akapustyanik/MZCAT/firmware/Cameras/tamples/right/original quality/h.bmp

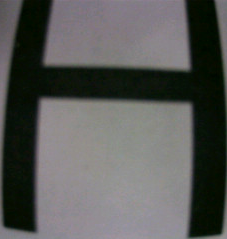
firmware/Cameras/tamples/right/original quality/h.bmp
