akapustyanik/MZCAT/firmware/Cameras/tamples/right/original quality/s.bmp

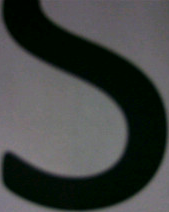
firmware/Cameras/tamples/right/original quality/s.bmp
