akapustyanik/MZCAT/firmware/Cameras/tamples/right/original quality/u.bmp

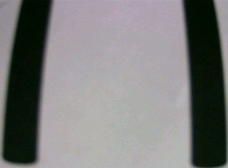
firmware/Cameras/tamples/right/original quality/u.bmp
