akapustyanik/MZCAT/firmware/Cameras/tamples/S_1.bmp

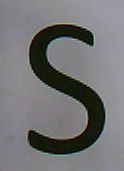
firmware/Cameras/tamples/S_1.bmp
