akapustyanik/MZCAT/photo/robot photo2.jpg

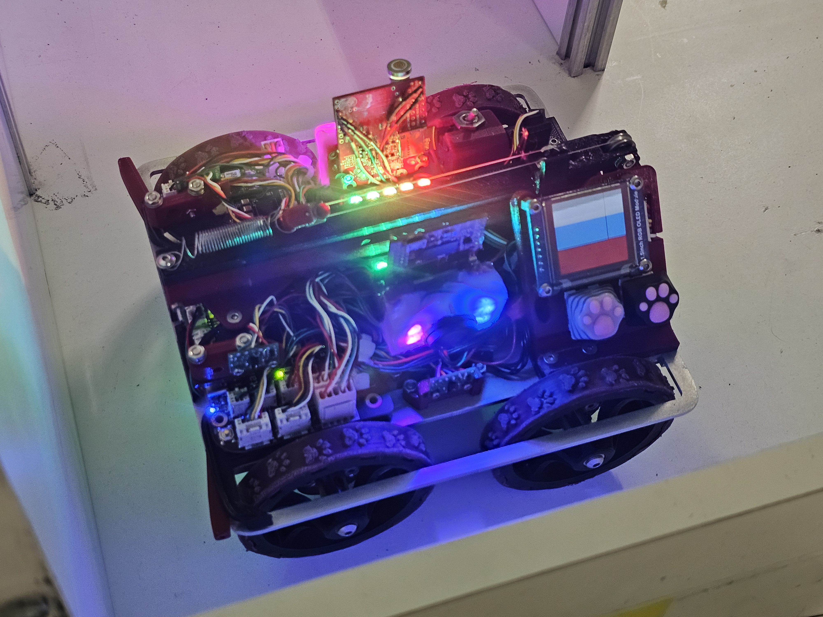
photo/robot photo2.jpg
