akapustyanik/MZCAT/photo/robot photo3.jpg

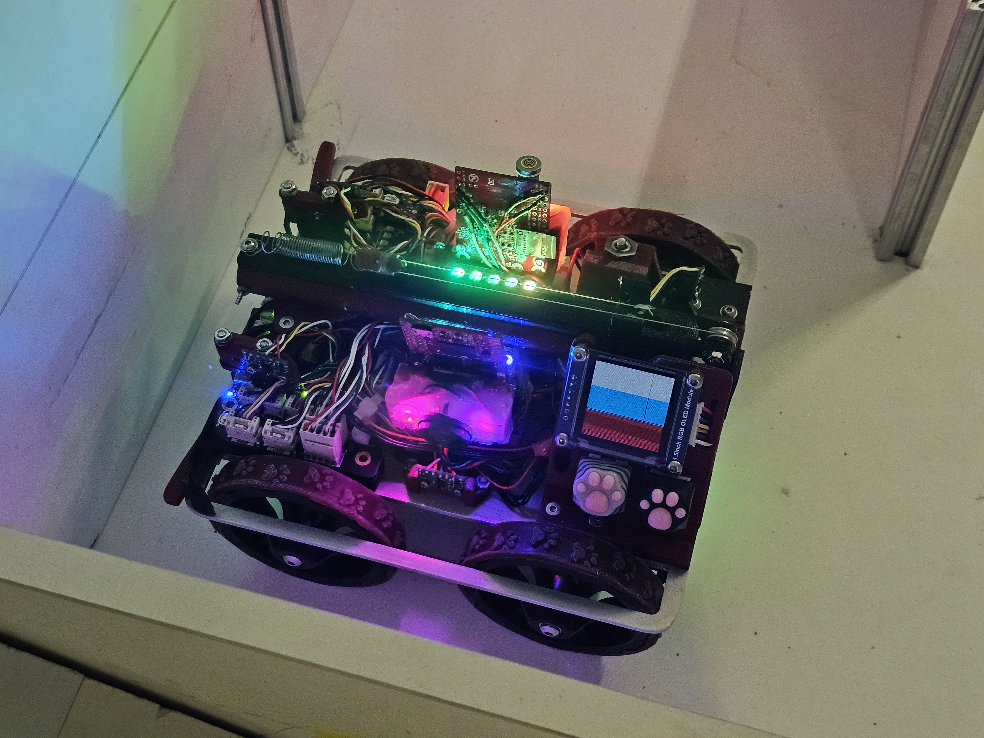
photo/robot photo3.jpg
