akapustyanik/MZCAT/photo/robot photo4.jpg

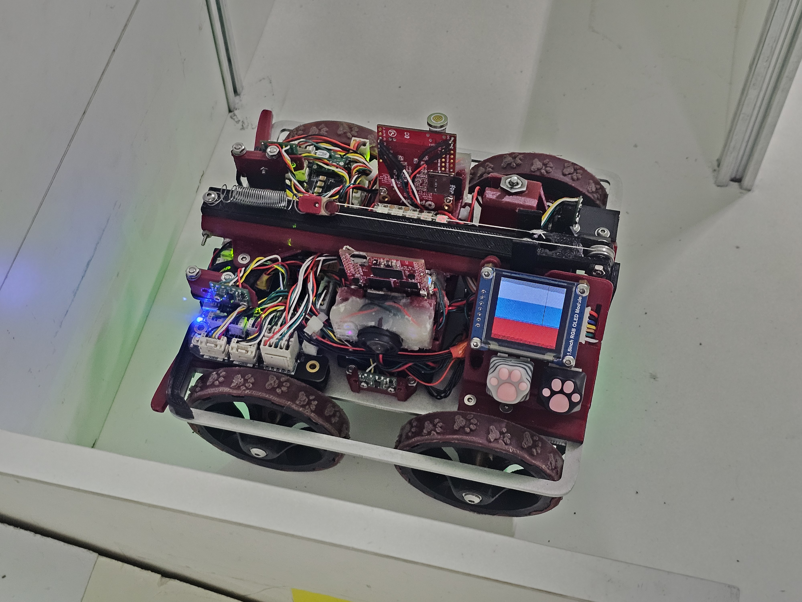
photo/robot photo4.jpg
