akapustyanik/MZCAT/photo/robot photo5.jpg

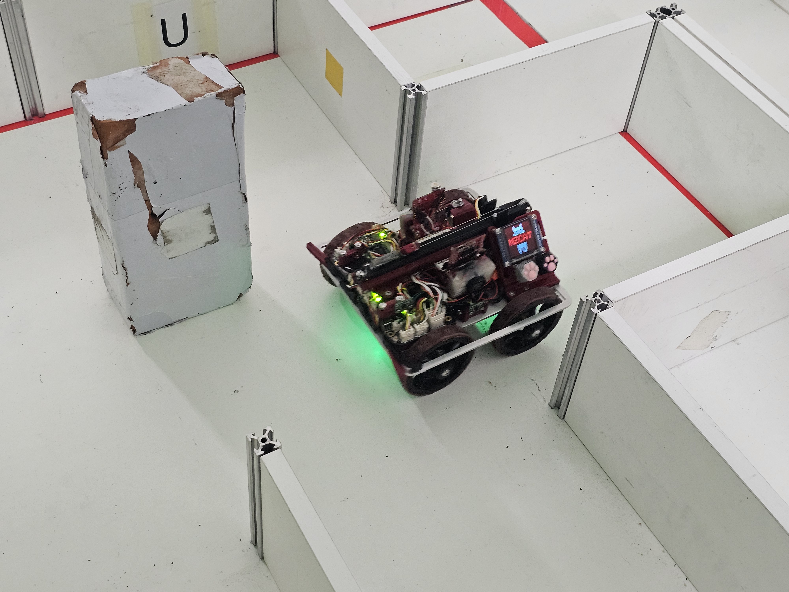
photo/robot photo5.jpg
