akapustyanik/MZCAT/photo/robot photo6.jpg

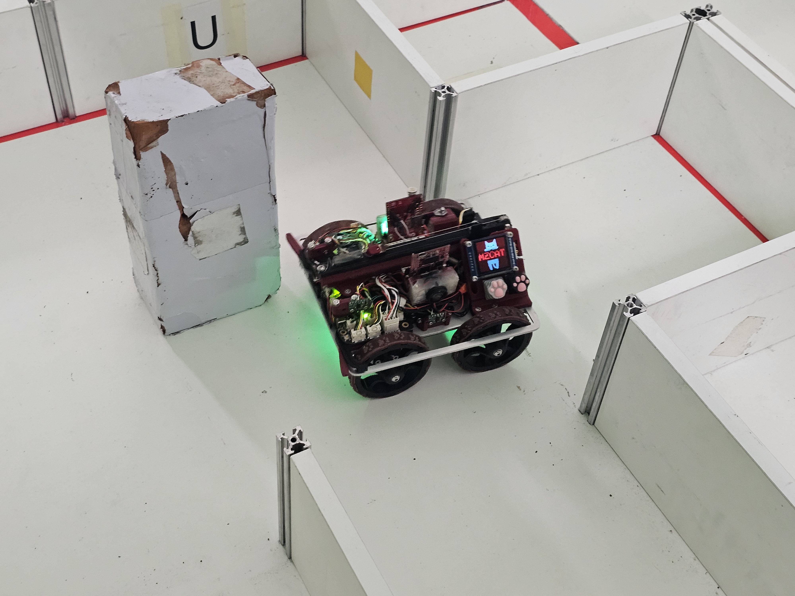
photo/robot photo6.jpg
