akapustyanik/MZCAT/photo/robot photo7.jpg

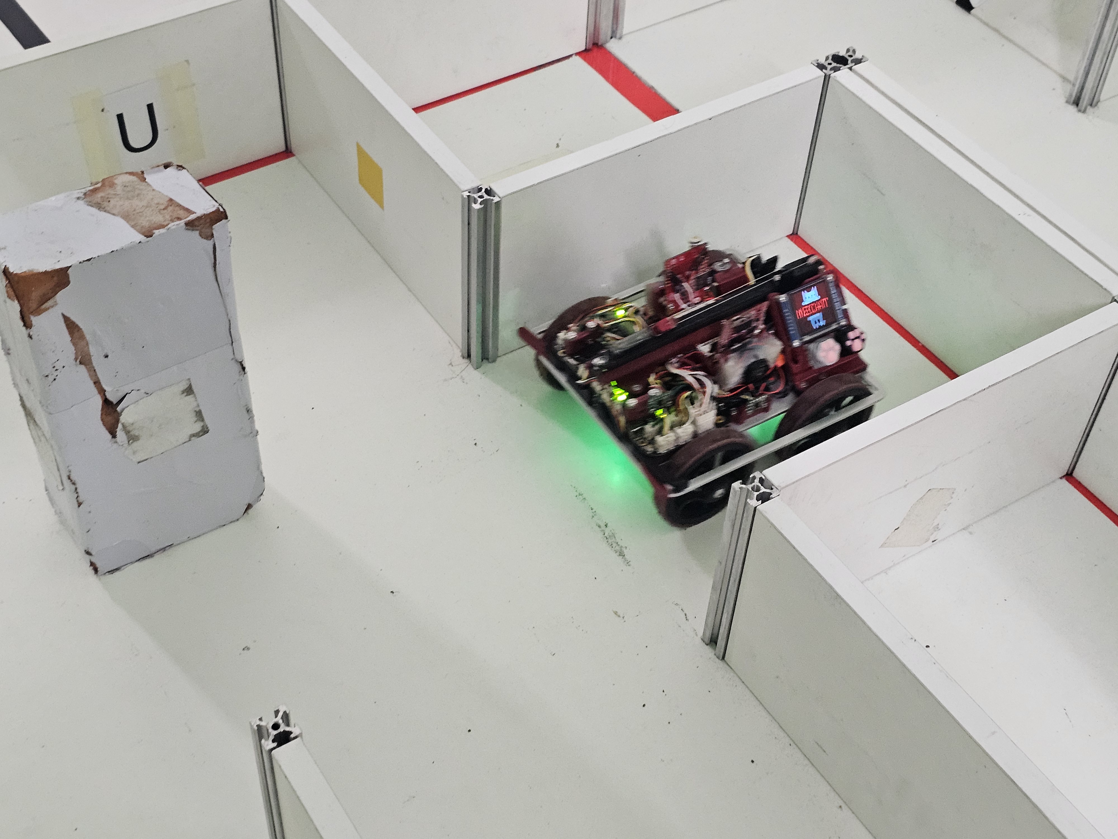
photo/robot photo7.jpg
