akapustyanik/MZCAT/photo/robot photo8.jpg

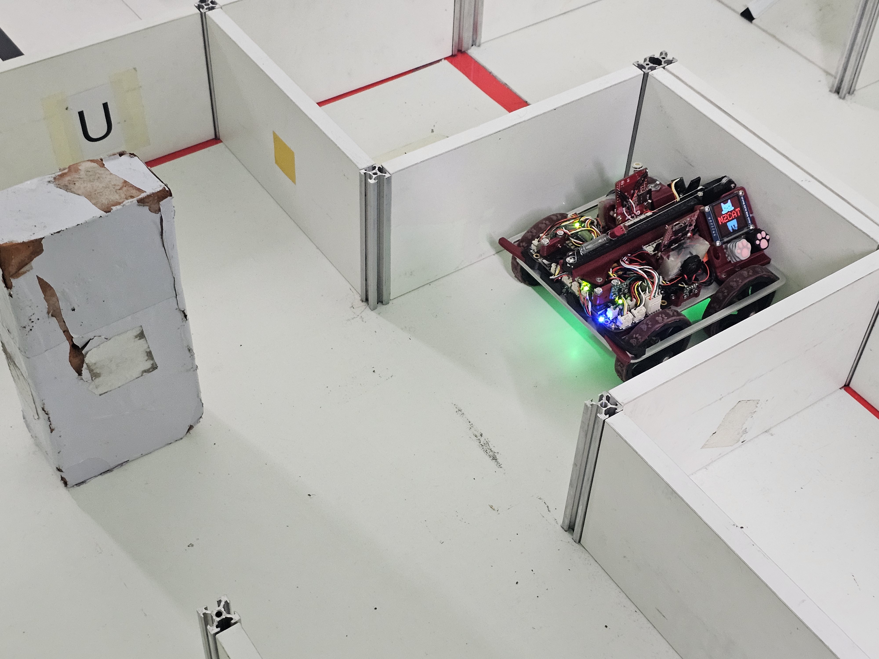
photo/robot photo8.jpg
