akapustyanik/MZCAT/photo/robot photo.jpg

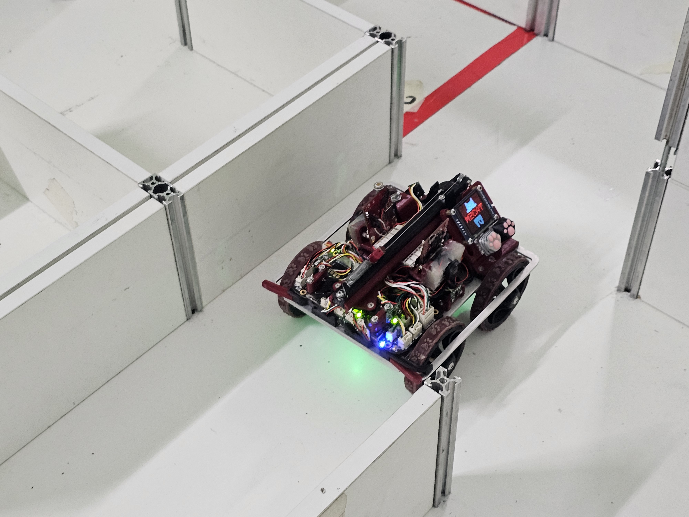
photo/robot photo.jpg
