akapustyanik/MZCAT/Construction/other_models/OpenMV H7/Components/Micro USB socket/UJ2-MIBH2-4-SMT_02.SLDPRT

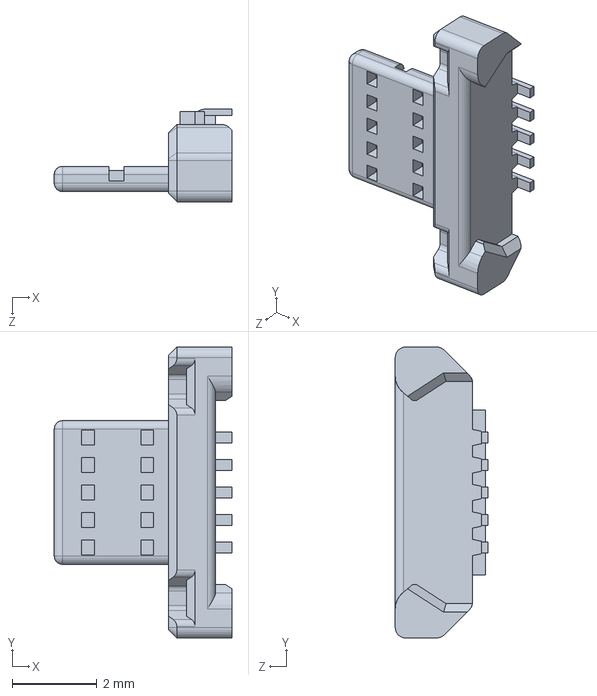
[picture p29: CAD file, 2024-03-27]
Construction/other_models/OpenMV H7/Components/Micro USB socket/UJ2-MIBH2-4-SMT_02.SLDPRT
4.20 x 6.88 x 2.19 mm
