akapustyanik/MZCAT/Construction/other_models/OpenMV H7/Components/standoffs/Standoff metal 5x2.5mm.SLDPRT

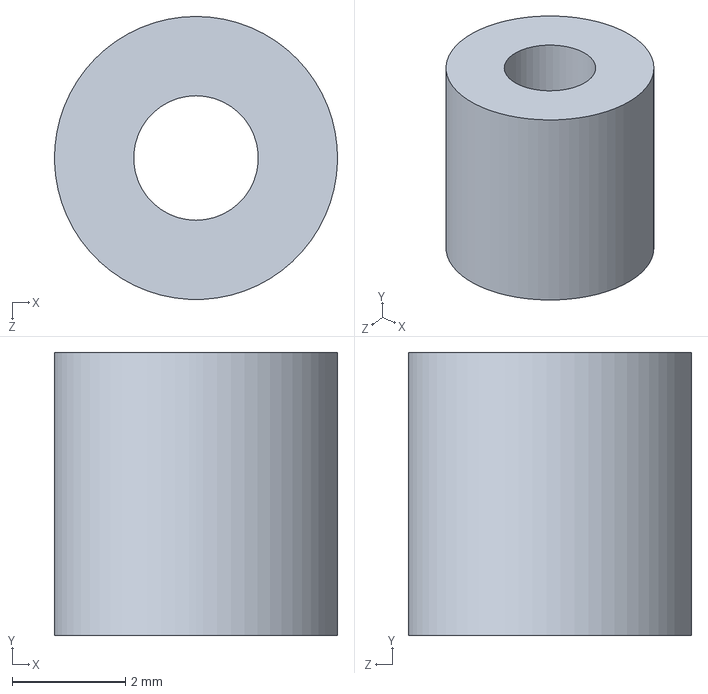
[picture p30: CAD file, 2024-03-27]
Construction/other_models/OpenMV H7/Components/standoffs/Standoff metal 5x2.5mm.SLDPRT
5.00 x 5.00 x 5.00 mm
