akapustyanik/MZCAT/Construction/other_models/OpenMV H7/Components/USB/Micro USB connector.SLDPRT

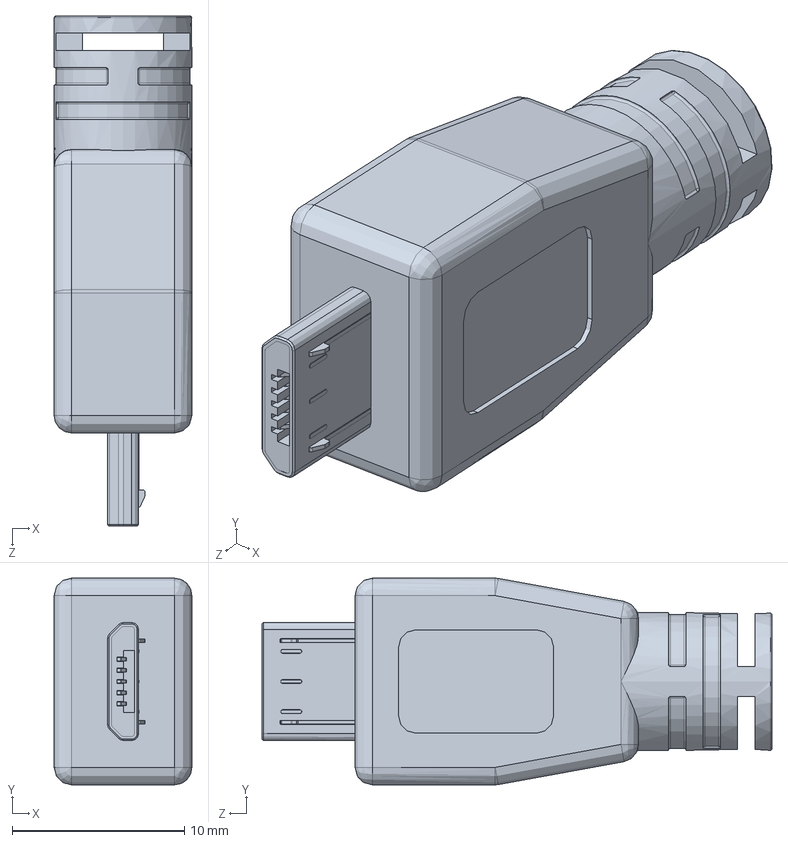
[picture p31: CAD file, 2024-03-27]
Construction/other_models/OpenMV H7/Components/USB/Micro USB connector.SLDPRT
8.00 x 12.0 x 29.6 mm
