akapustyanik/MZCAT/Construction/other_models/vl53l0x/vl53l0x no headers.STEP

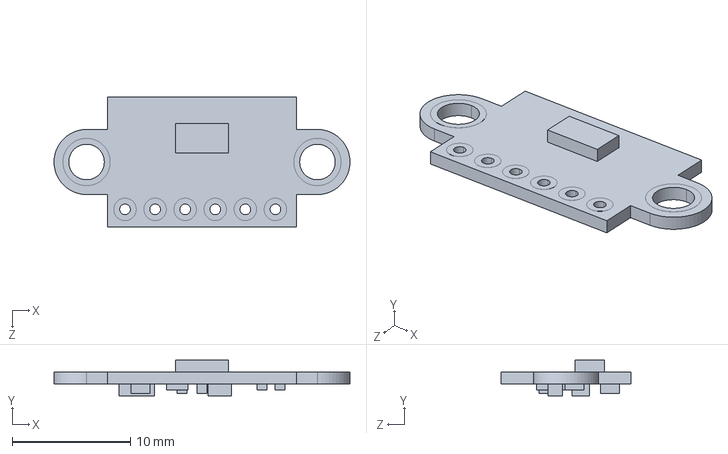
[picture p32: CAD file, 2024-03-27]
Construction/other_models/vl53l0x/vl53l0x no headers.STEP
25.0 x 3.00 x 11.0 mm
