akapustyanik/MZCAT/Construction/step/User Library-xt30-f.step

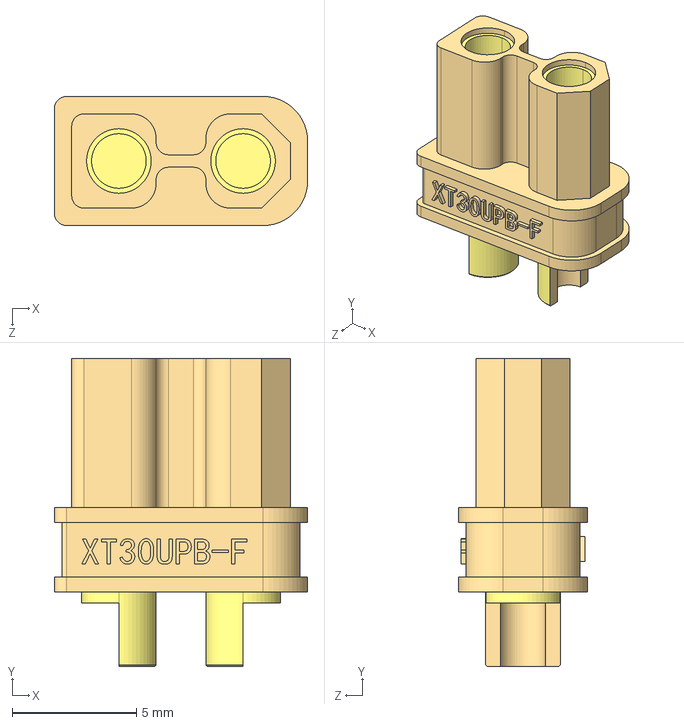
[picture p33: CAD file, 2024-03-27]
Construction/step/User Library-xt30-f.step
10.2 x 12.4 x 5.20 mm
