akapustyanik/MZCAT/Construction/stl/karetka.stl

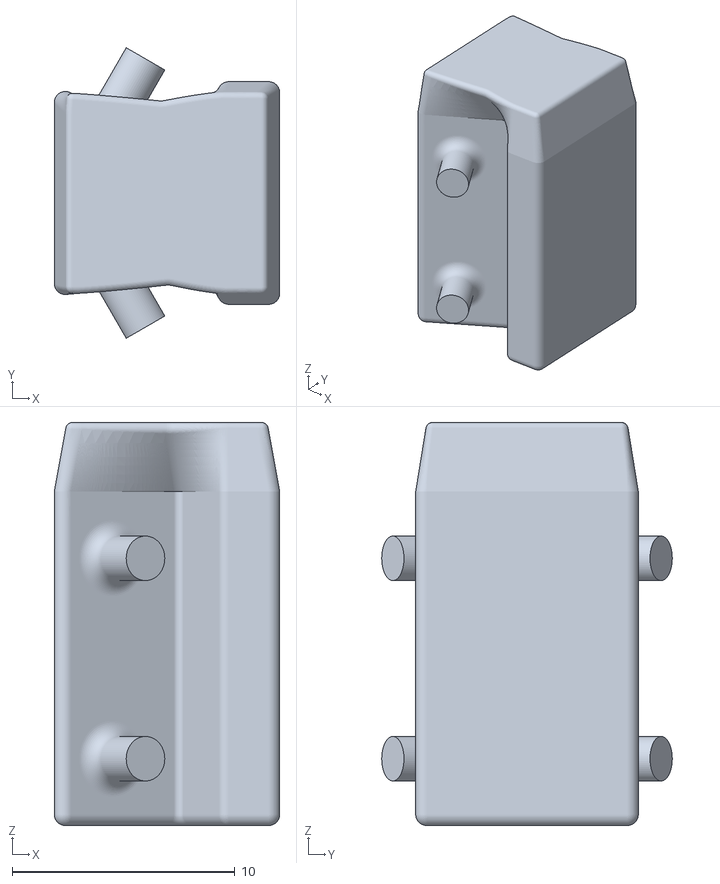
[picture p34: CAD file, 2024-03-27]
Construction/stl/karetka.stl
10.1 x 13.0 x 18.1
