akapustyanik/MZCAT/Construction/dxf/maze_4.dxf

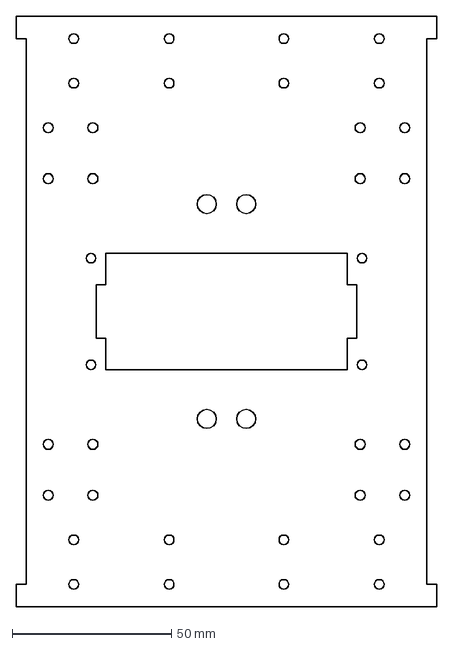
[picture p35: CAD file, 2024-03-27]
Construction/dxf/maze_4.dxf
132.0 x 185.5 mm
