akapustyanik/MZCAT/Construction/other_models/OpenMV H7/Boards/ov7725.sldprt

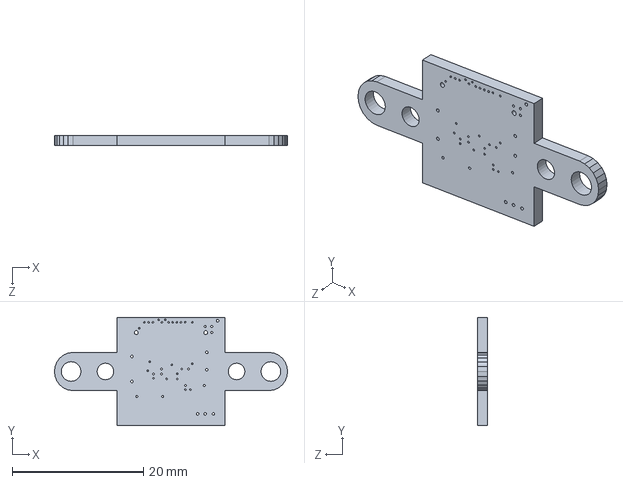
[picture p36: CAD file, 2024-03-27]
Construction/other_models/OpenMV H7/Boards/ov7725.sldprt
35.6 x 16.5 x 1.60 mm
