akapustyanik/MZCAT/Construction/other_models/OpenMV H7/Components/Camera_20mm/mount_lens.SLDPRT

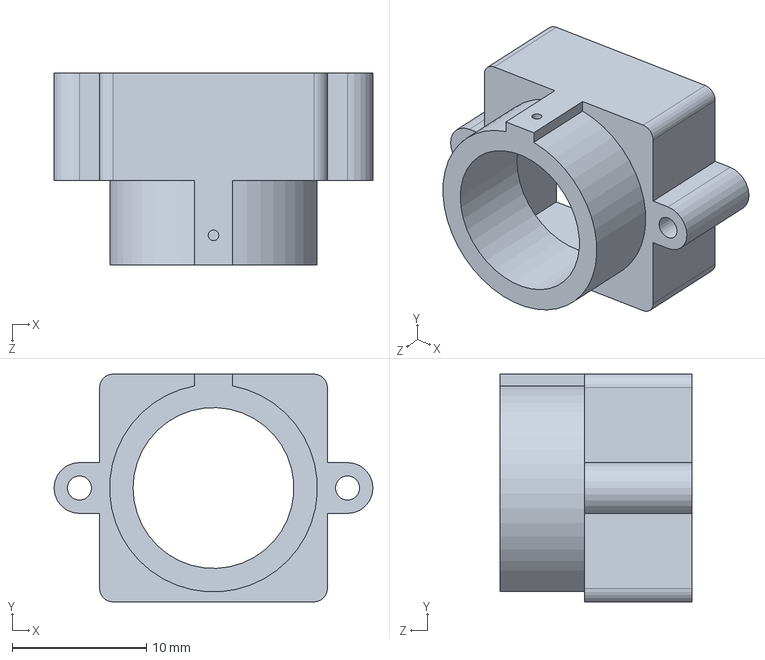
[picture p37: CAD file, 2024-03-27]
Construction/other_models/OpenMV H7/Components/Camera_20mm/mount_lens.SLDPRT
23.8 x 17.0 x 14.3 mm
