akapustyanik/MZCAT/Construction/other_models/OpenMV H7/Components/Micro USB socket/UJ2-MIBH2-4-SMT_01.SLDPRT

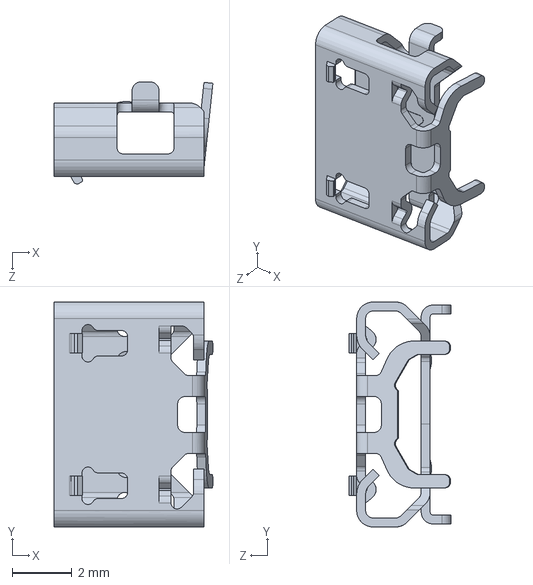
[picture p38: CAD file, 2024-03-27]
Construction/other_models/OpenMV H7/Components/Micro USB socket/UJ2-MIBH2-4-SMT_01.SLDPRT
5.29 x 7.50 x 3.41 mm
