akapustyanik/MZCAT/Construction/other_models/OpenMV H7/Components/Resistor 0603.SLDPRT

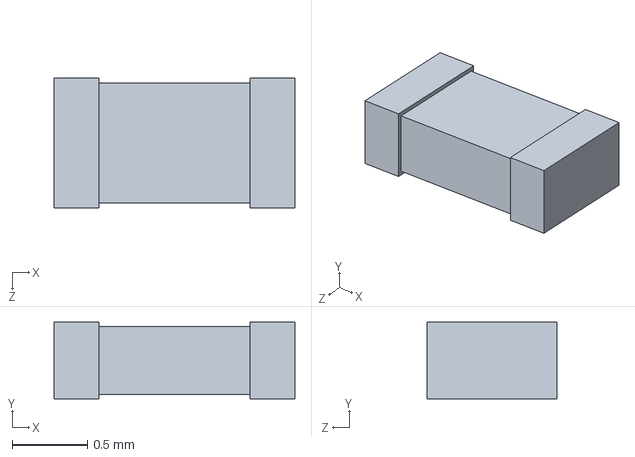
[picture p39: CAD file, 2024-03-27]
Construction/other_models/OpenMV H7/Components/Resistor 0603.SLDPRT
1.60 x 0.51 x 0.86 mm
