akapustyanik/MZCAT/Construction/other_models/OpenMV H7/Components/USB/Micro USB connector angle.SLDPRT

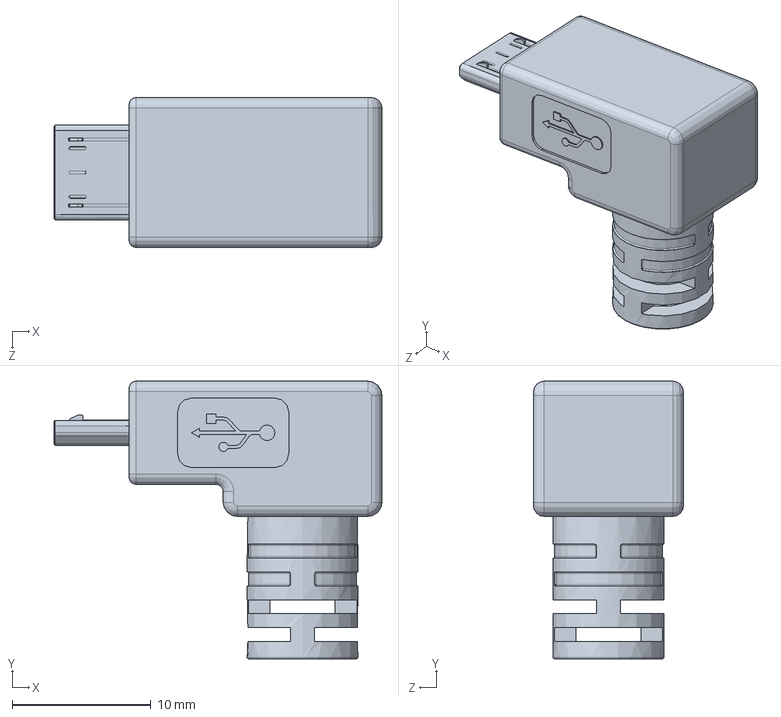
[picture p40: CAD file, 2024-03-27]
Construction/other_models/OpenMV H7/Components/USB/Micro USB connector angle.SLDPRT
23.6 x 20.0 x 10.8 mm
