akapustyanik/MZCAT/Construction/other_models/vl53l0x/pin_header.SLDPRT

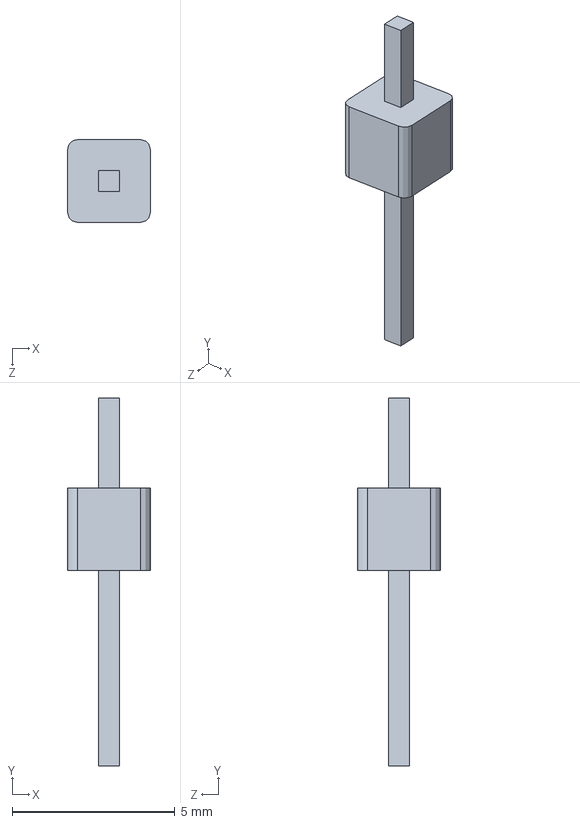
[picture p41: CAD file, 2024-03-27]
Construction/other_models/vl53l0x/pin_header.SLDPRT
2.54 x 11.3 x 2.54 mm
