akapustyanik/MZCAT/Construction/step/kicad_module_3D_MINI560.step

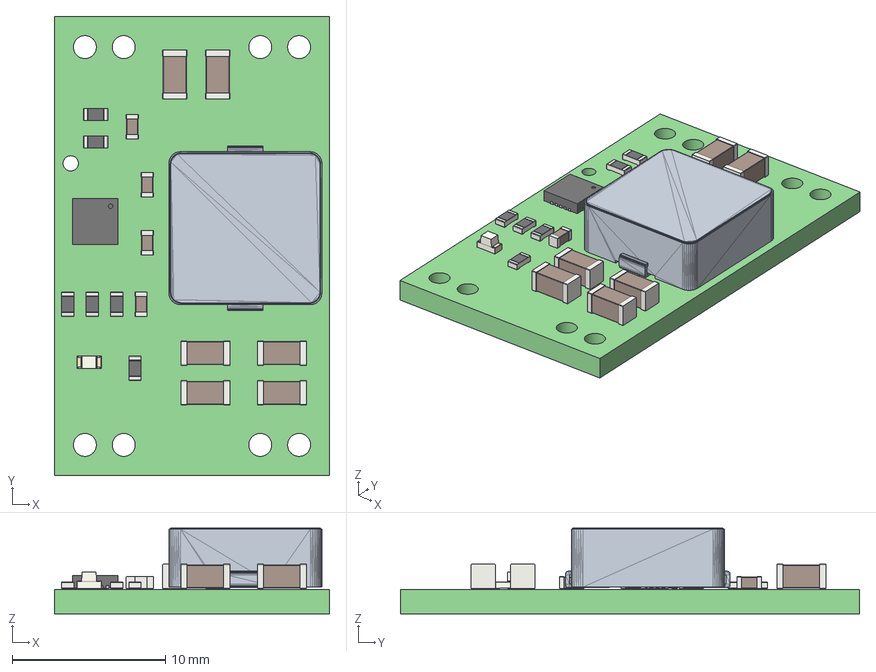
[picture p42: CAD file, 2024-03-27]
Construction/step/kicad_module_3D_MINI560.step
18.0 x 30.0 x 5.62 mm
kicad_module_3D_MINI560 PCB
