akapustyanik/MZCAT/Construction/stl/разделитель.stl

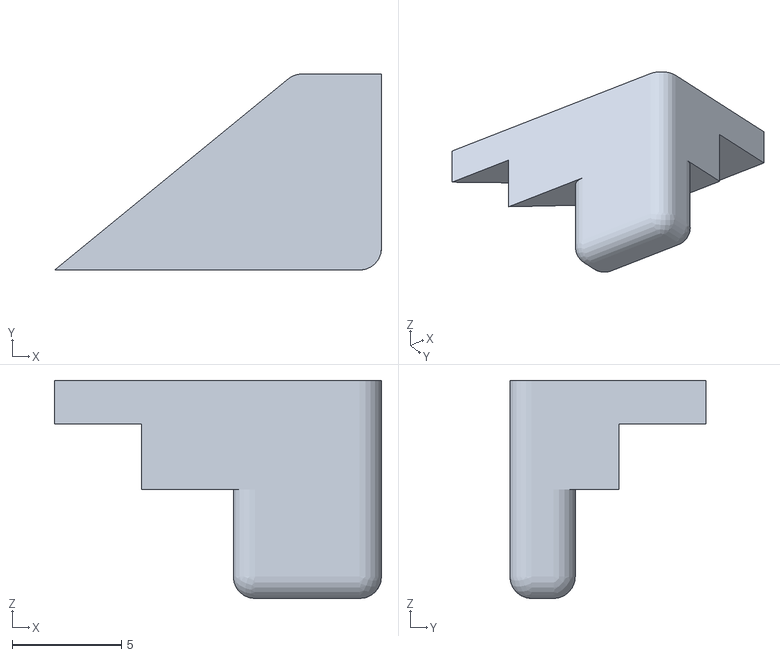
[picture p43: CAD file, 2024-03-27]
Construction/stl/разделитель.stl
15.0 x 9.00 x 10.0
