akapustyanik/MZCAT/Construction/dxf/holder.dxf

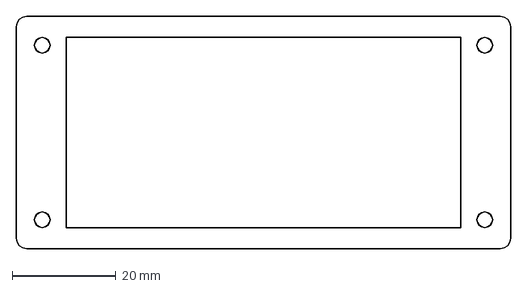
[picture p44: CAD file, 2024-03-27]
Construction/dxf/holder.dxf
95.2 x 44.7 mm
