akapustyanik/MZCAT/Construction/other_models/OpenMV H7/Components/Camera_20mm/LENS_Standard.SLDPRT

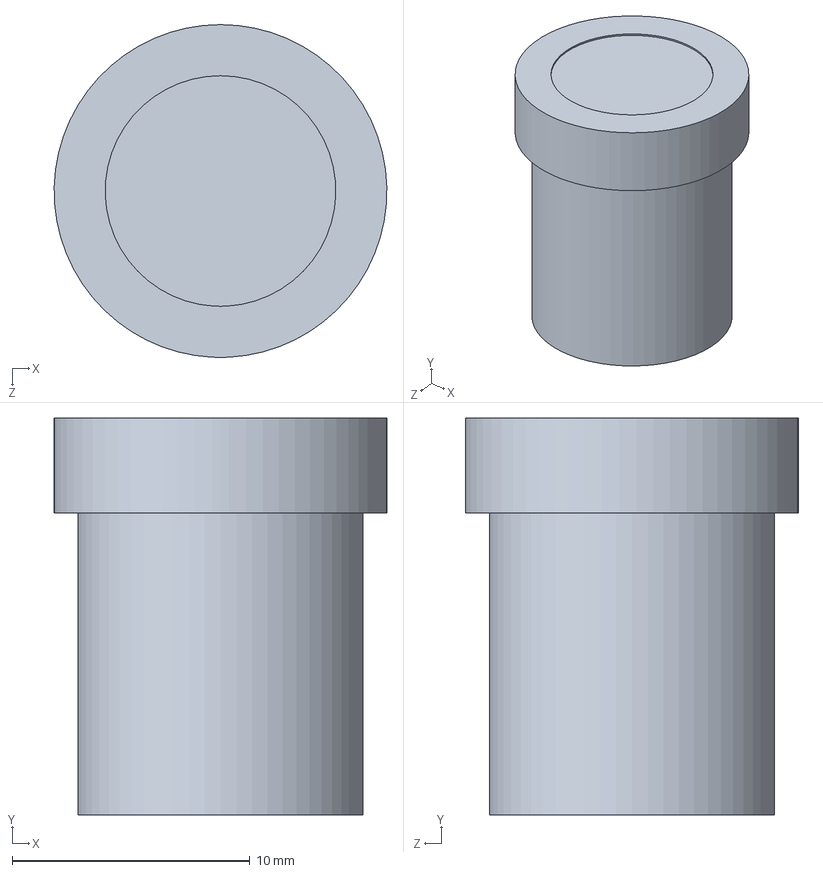
[picture p45: CAD file, 2024-03-27]
Construction/other_models/OpenMV H7/Components/Camera_20mm/LENS_Standard.SLDPRT
14.0 x 16.7 x 14.0 mm
