akapustyanik/MZCAT/Construction/other_models/OpenMV H7/Components/LED 1206 IR.SLDPRT

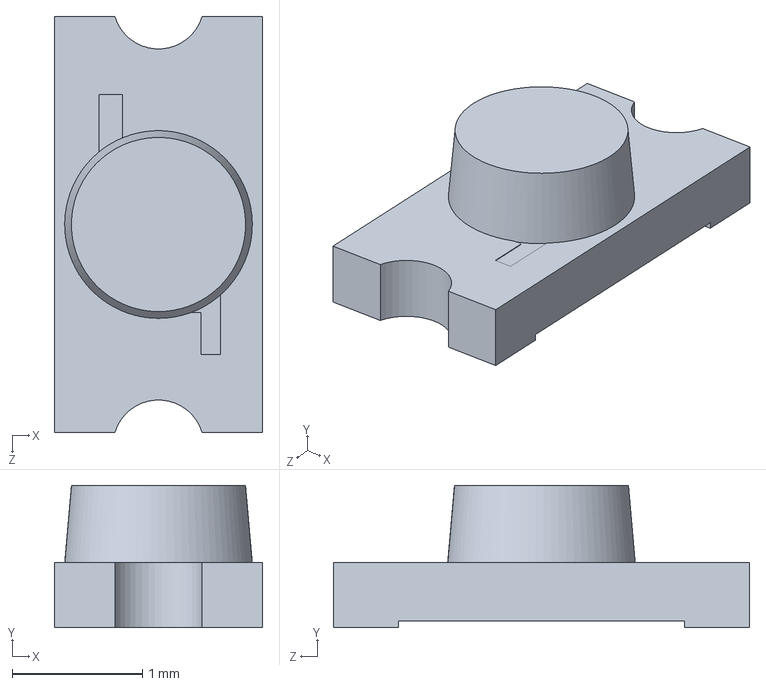
[picture p46: CAD file, 2024-03-27]
Construction/other_models/OpenMV H7/Components/LED 1206 IR.SLDPRT
1.60 x 1.09 x 3.20 mm
