akapustyanik/MZCAT/Construction/other_models/vl53l0x/vl53l0x.STEP

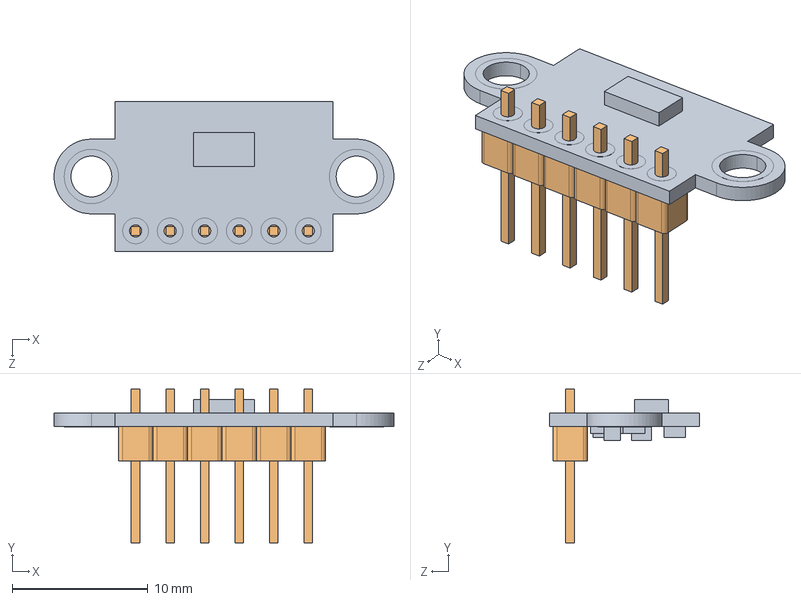
[picture p47: CAD file, 2024-03-27]
Construction/other_models/vl53l0x/vl53l0x.STEP
25.0 x 11.3 x 11.0 mm
vl53l0x_PCB
pin_header x 6
