akapustyanik/MZCAT/Construction/step/clik mate 3.stp

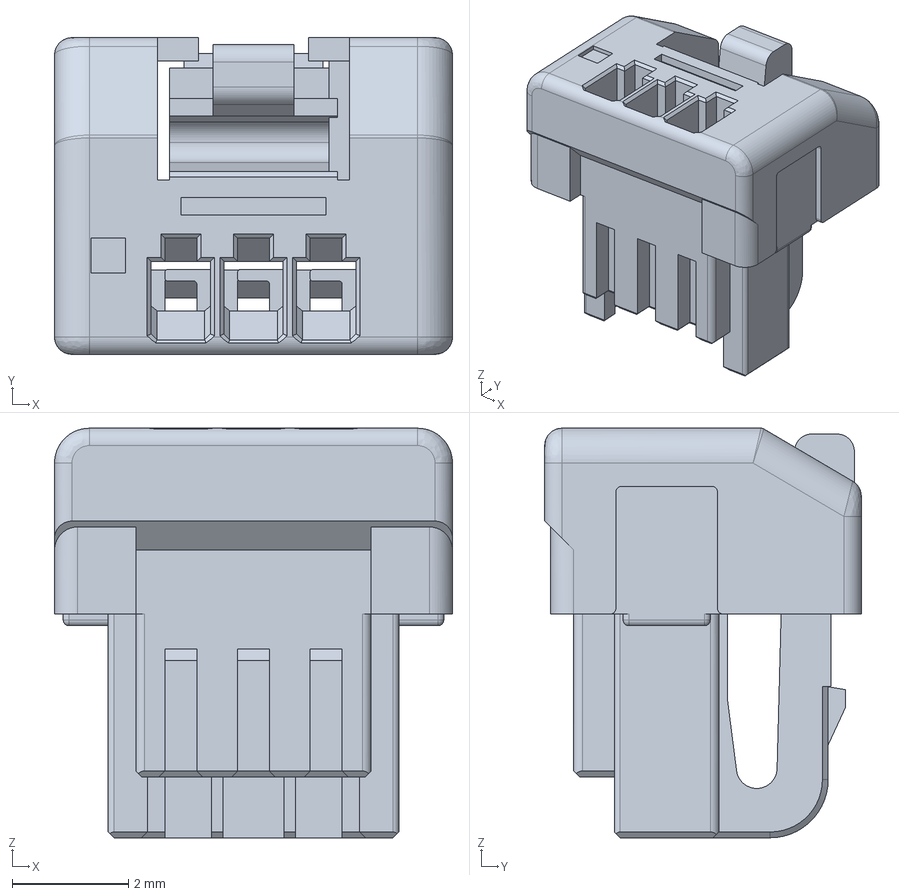
[picture p48: CAD file, 2024-03-27]
Construction/step/clik mate 3.stp
6.85 x 5.45 x 7.05 mm
