akapustyanik/MZCAT/Construction/stl/laser_krepl_2.stl

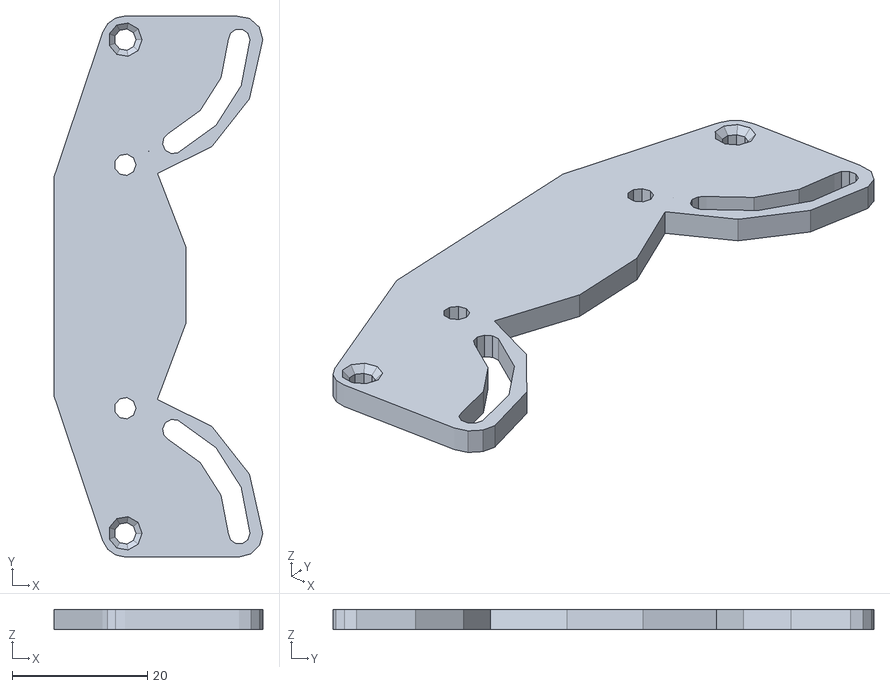
[picture p49: CAD file, 2024-03-27]
Construction/stl/laser_krepl_2.stl
30.9 x 80.0 x 3.00
