akapustyanik/MZCAT/Construction/dxf/protection_frame2.dxf

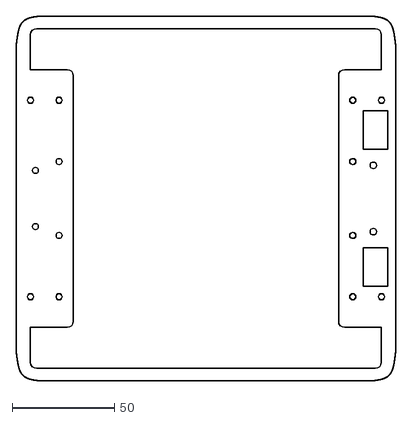
[picture p50: CAD file, 2024-03-27]
Construction/dxf/protection_frame2.dxf
185.5 x 178.0
