akapustyanik/MZCAT/Construction/step/light_sensor.step

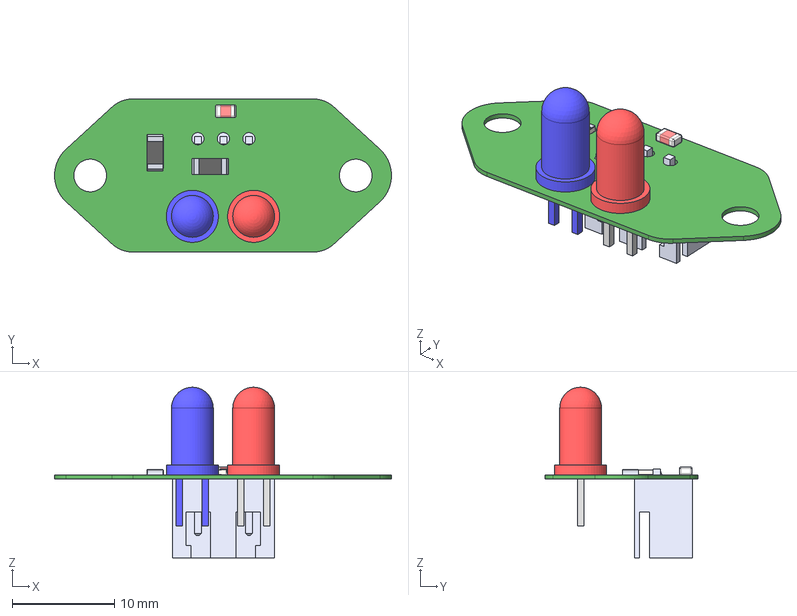
[picture p51: CAD file, 2024-03-27]
Construction/step/light_sensor.step
33.0 x 15.0 x 16.7 mm
SW3DPS-5MM_LED_RED-DEFAULT
CAP0805
SW3DPS-5MM_LED_RED-DEFAULT_RGB16711680
R1206 x 2
CWF_3_V
