akapustyanik/MZCAT/Construction/stl/end cap left.stl

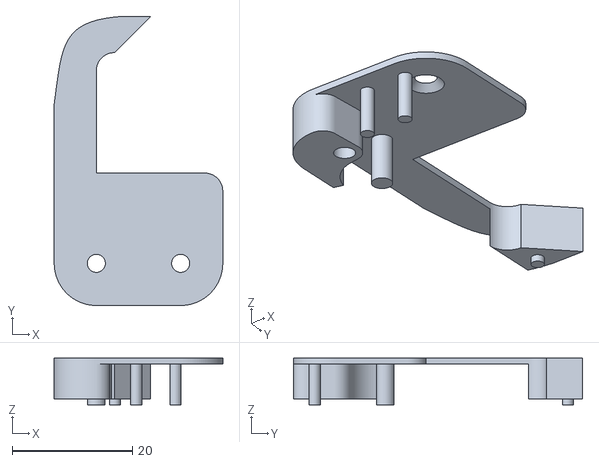
[picture p52: CAD file, 2024-03-27]
Construction/stl/end cap left.stl
28.0 x 48.0 x 7.80
