akapustyanik/MZCAT/Construction/dxf/osvesh2.dxf

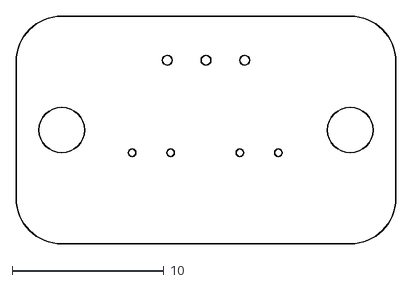
[picture p53: CAD file, 2024-03-27]
Construction/dxf/osvesh2.dxf
25.0 x 15.0
