akapustyanik/MZCAT/Construction/other_models/OpenMV H7/Components/S2B-PH-K-S(LF)(SN).SLDPRT

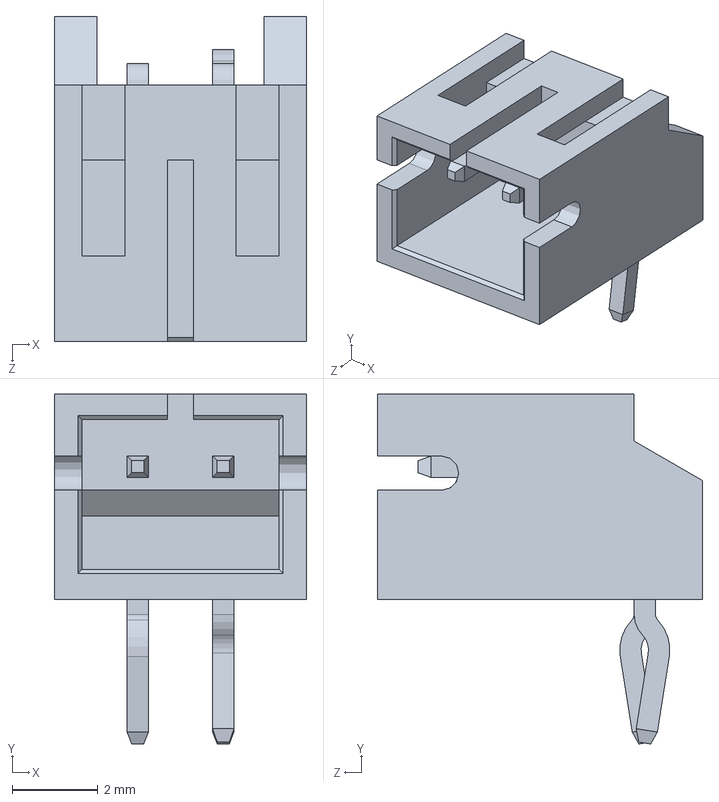
[picture p54: CAD file, 2024-03-27]
Construction/other_models/OpenMV H7/Components/S2B-PH-K-S(LF)(SN).SLDPRT
5.90 x 8.18 x 7.60 mm
