akapustyanik/MZCAT/Construction/stl/pizza_2.stl

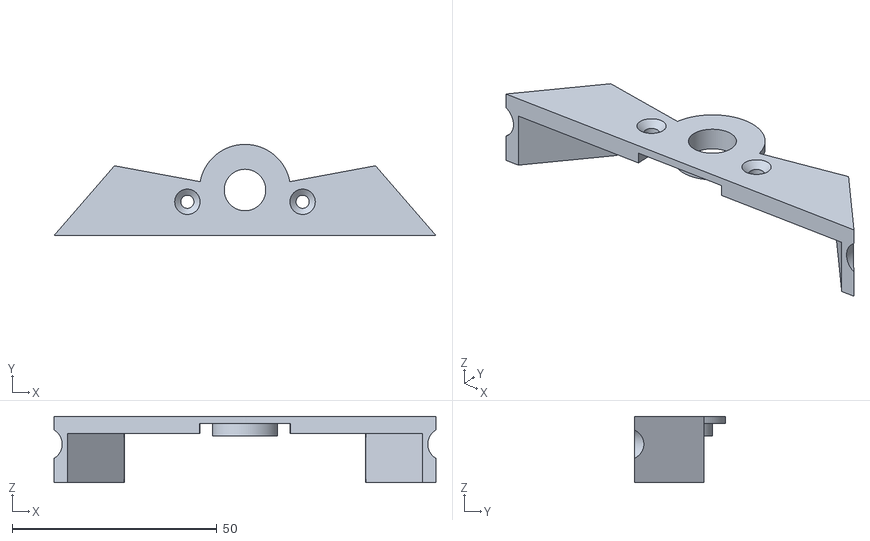
[picture p55: CAD file, 2024-03-27]
Construction/stl/pizza_2.stl
93.4 x 22.3 x 16.2
