akapustyanik/MZCAT/Construction/dxf/osvesh4.dxf

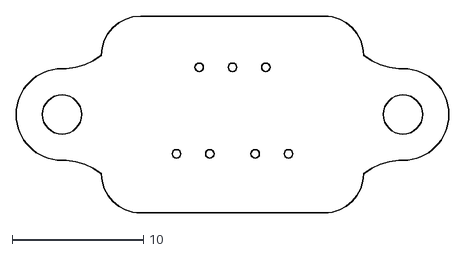
[picture p56: CAD file, 2024-03-27]
Construction/dxf/osvesh4.dxf
33.0 x 15.0
