akapustyanik/MZCAT/Construction/other_models/OpenMV H7/Components/DF1236.SLDPRT

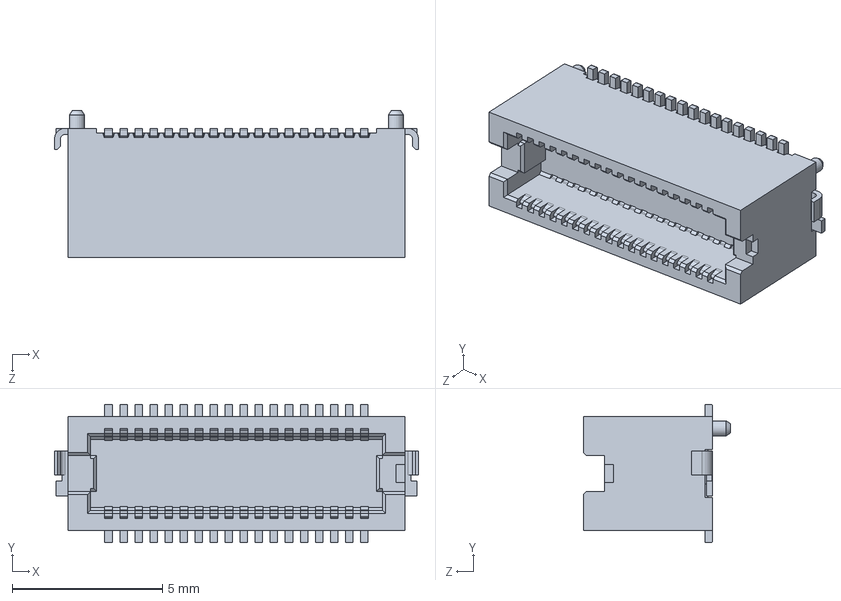
[picture p57: CAD file, 2024-03-27]
Construction/other_models/OpenMV H7/Components/DF1236.SLDPRT
12.1 x 4.60 x 4.90 mm
