akapustyanik/MZCAT/Construction/step/clik maate 7.stp

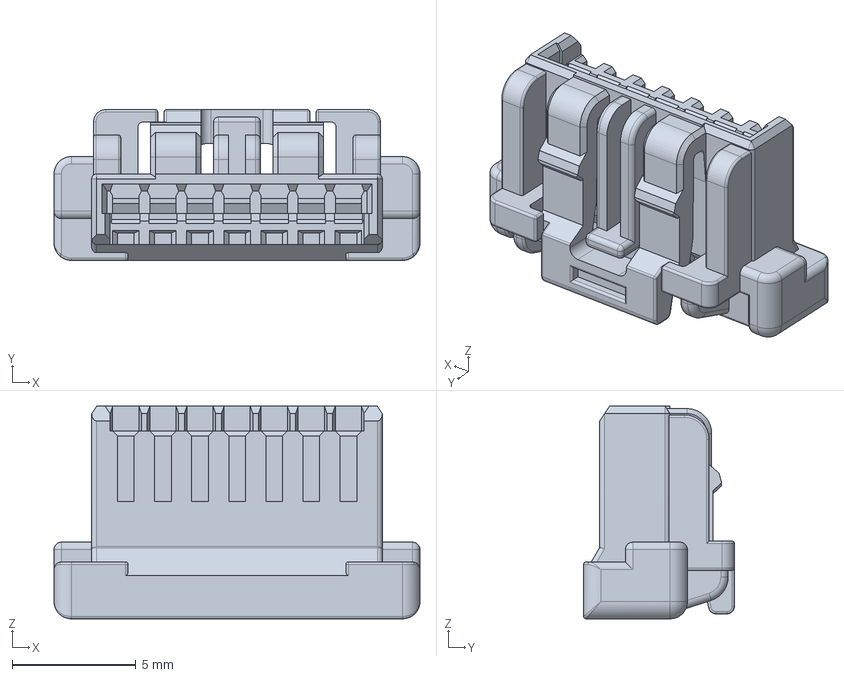
[picture p58: CAD file, 2024-03-27]
Construction/step/clik maate 7.stp
14.8 x 6.10 x 8.60 mm
