akapustyanik/MZCAT/Construction/stl/akkum3_shelki_claw1.stl

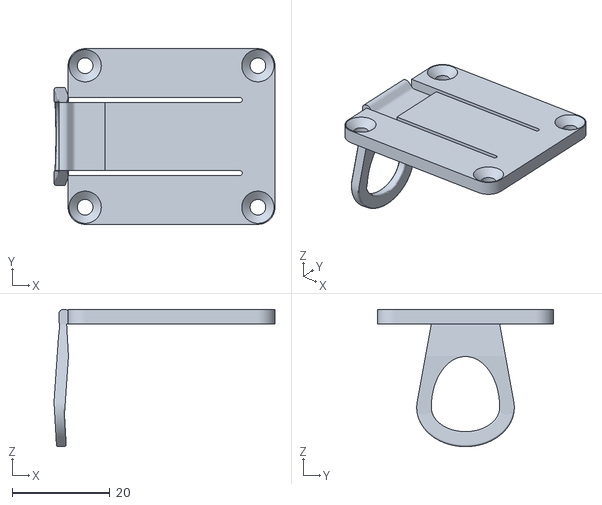
[picture p59: CAD file, 2024-03-27]
Construction/stl/akkum3_shelki_claw1.stl
45.3 x 36.0 x 28.1
