akapustyanik/MZCAT/Construction/dxf/osvesh3.dxf

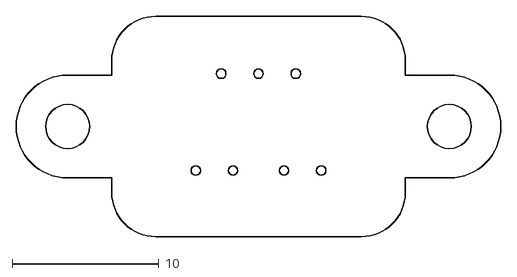
[picture p60: CAD file, 2024-03-27]
Construction/dxf/osvesh3.dxf
33.0 x 15.0
