akapustyanik/MZCAT/Construction/step/lazer_side.stp

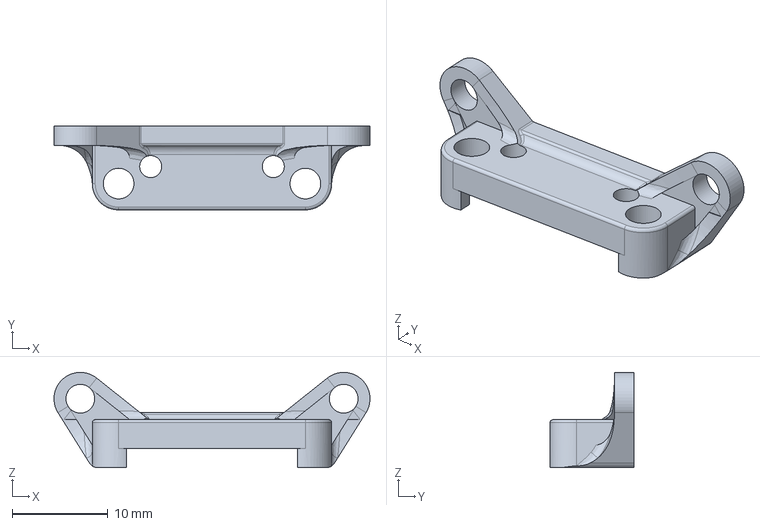
[picture p62: CAD file, 2024-03-27]
Construction/step/lazer_side.stp
33.0 x 8.75 x 9.94 mm
