akapustyanik/MZCAT/Construction/dxf/maze_04.dxf

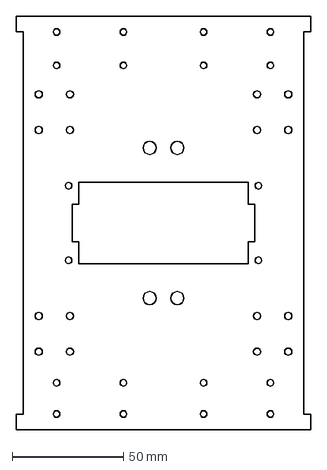
[picture p63: CAD file, 2024-03-27]
Construction/dxf/maze_04.dxf
132.0 x 185.5 mm
