akapustyanik/MZCAT/Construction/other_models/OpenMV H7/Components/1206.SLDPRT

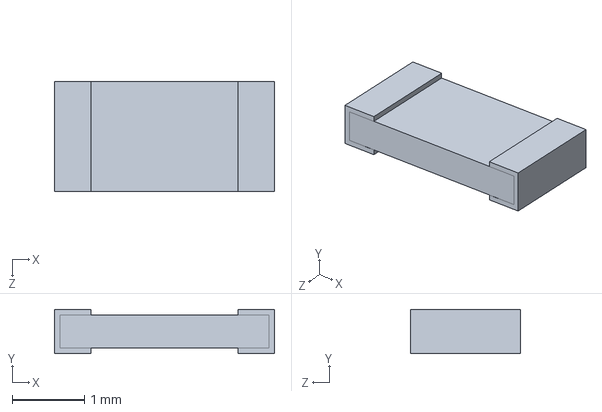
[picture p64: CAD file, 2024-03-27]
Construction/other_models/OpenMV H7/Components/1206.SLDPRT
3.05 x 0.61 x 1.53 mm
