akapustyanik/MZCAT/Construction/step/clik mate 6.stp

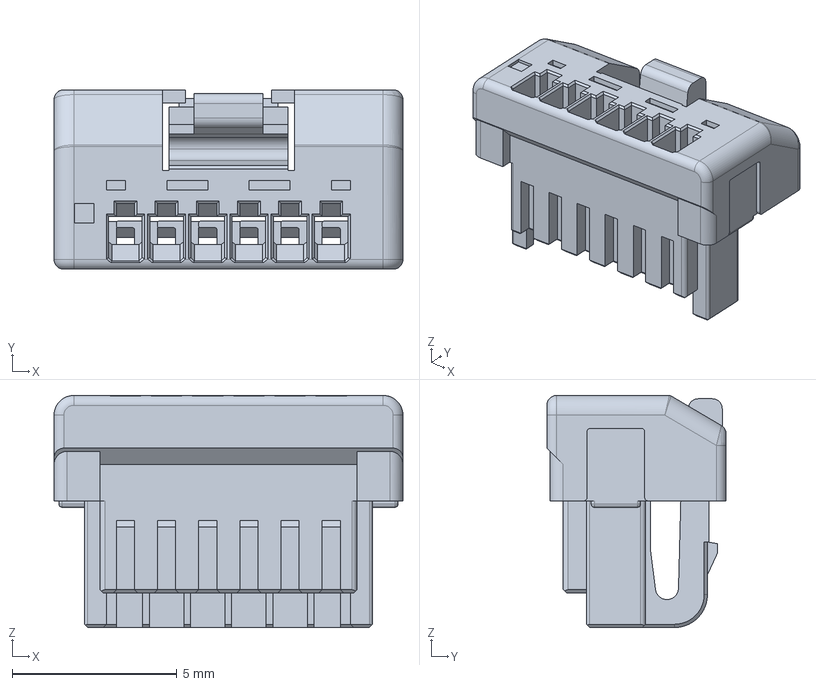
[picture p65: CAD file, 2024-03-27]
Construction/step/clik mate 6.stp
10.6 x 5.45 x 7.05 mm
