akapustyanik/MZCAT/Construction/stl/wheel_1.stl

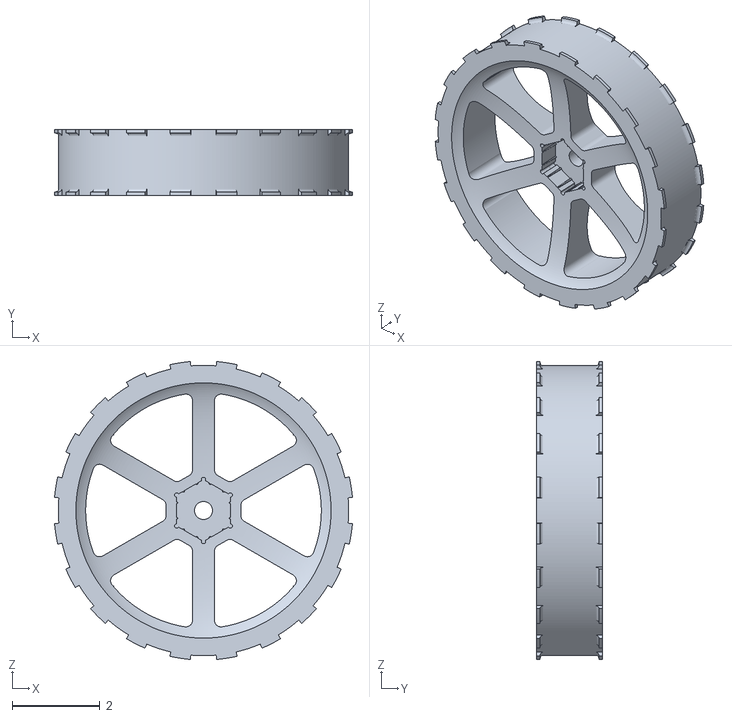
[picture p66: CAD file, 2024-03-27]
Construction/stl/wheel_1.stl
6.77 x 1.50 x 6.77
