akapustyanik/MZCAT/Construction/dxf/motherboard_countour.dxf

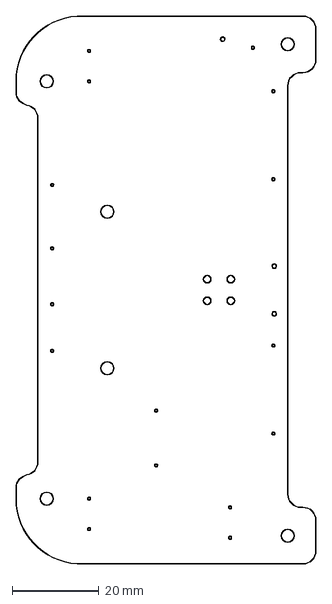
[picture p67: CAD file, 2024-03-27]
Construction/dxf/motherboard_countour.dxf
69.0 x 126.0 mm
