akapustyanik/MZCAT/Construction/other_models/OpenMV H7/Components/cap3216h160.SLDPRT

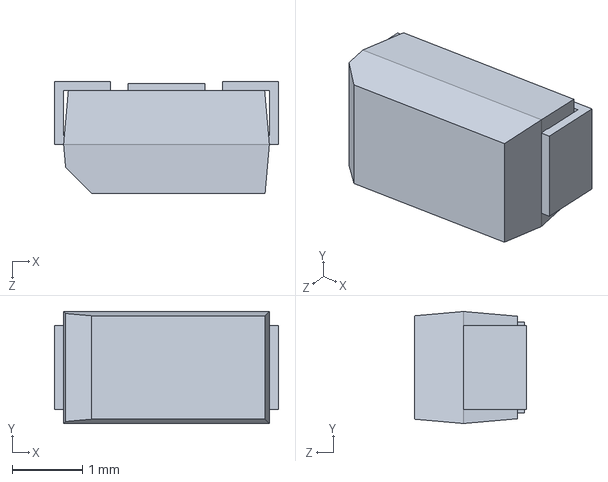
[picture p68: CAD file, 2024-03-27]
Construction/other_models/OpenMV H7/Components/cap3216h160.SLDPRT
3.20 x 1.60 x 1.60 mm
