akapustyanik/MZCAT/Construction/step/clik mate 2.stp

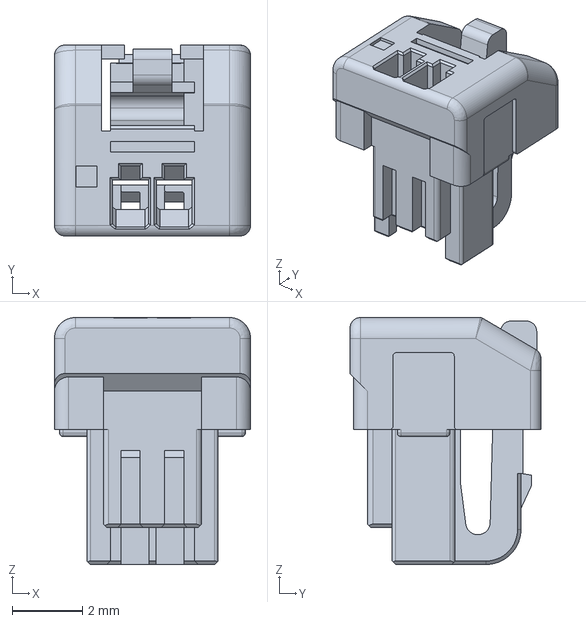
[picture p69: CAD file, 2024-03-27]
Construction/step/clik mate 2.stp
5.60 x 5.45 x 7.05 mm
