akapustyanik/MZCAT/Construction/stl/vydacha_4.stl

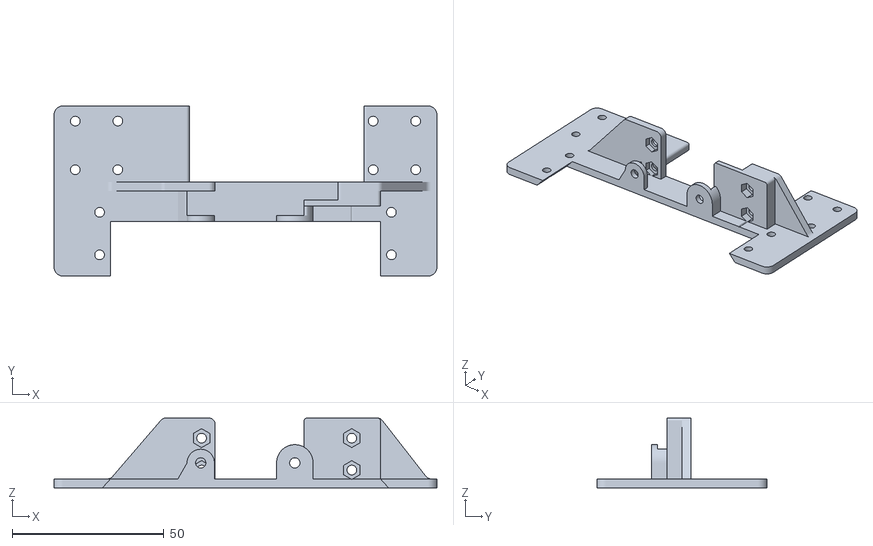
[picture p70: CAD file, 2024-03-27]
Construction/stl/vydacha_4.stl
126.0 x 56.0 x 23.0
