akapustyanik/MZCAT/Construction/dxf/frame.dxf

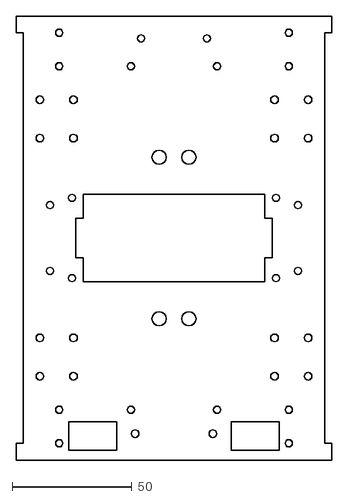
[picture p71: CAD file, 2024-03-27]
Construction/dxf/frame.dxf
132.0 x 185.5
