akapustyanik/MZCAT/Construction/step/c-1375820-9-a-3d.stp

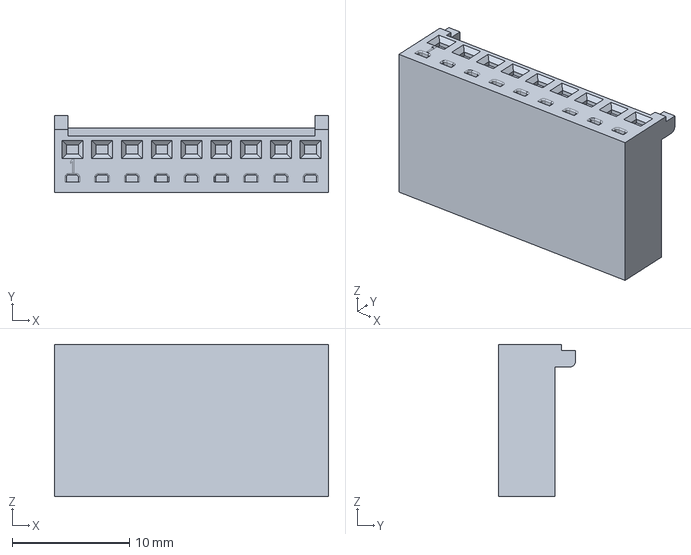
[picture p73: CAD file, 2024-03-27]
Construction/step/c-1375820-9-a-3d.stp
23.4 x 6.60 x 13.0 mm
