akapustyanik/MZCAT/Construction/dxf/led_5mm.dxf

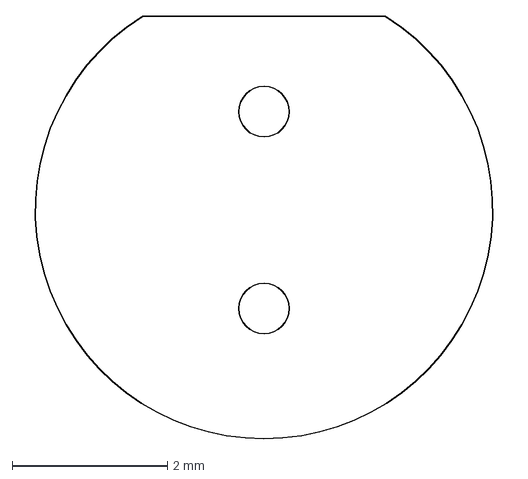
[picture p74: CAD file, 2024-03-27]
Construction/dxf/led_5mm.dxf
6.40 x 5.45 mm
