akapustyanik/MZCAT/Construction/other_models/OpenMV H7/Components/C0805K_C0805K.SLDPRT

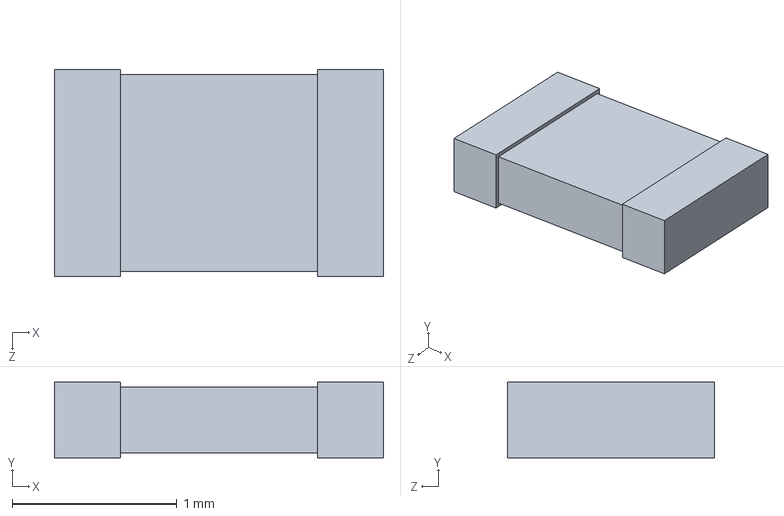
[picture p75: CAD file, 2024-03-27]
Construction/other_models/OpenMV H7/Components/C0805K_C0805K.SLDPRT
2.00 x 0.46 x 1.26 mm
