akapustyanik/MZCAT/Construction/step/clik mate 4.stp

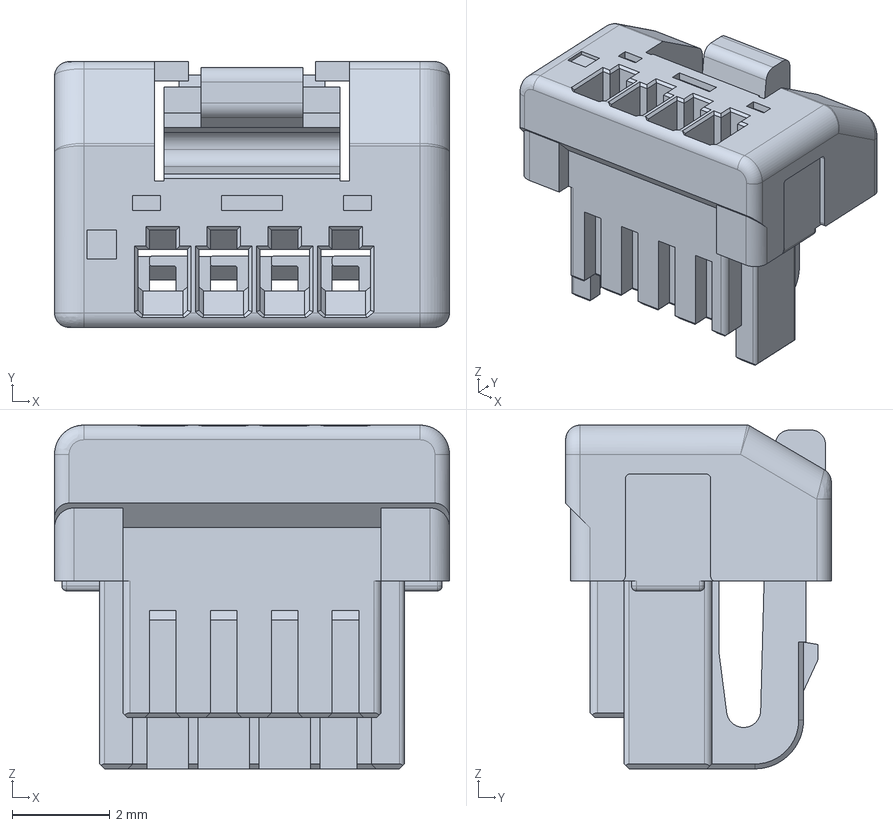
[picture p76: CAD file, 2024-03-27]
Construction/step/clik mate 4.stp
8.10 x 5.45 x 7.05 mm
