akapustyanik/MZCAT/Construction/stl/wheel_5.stl

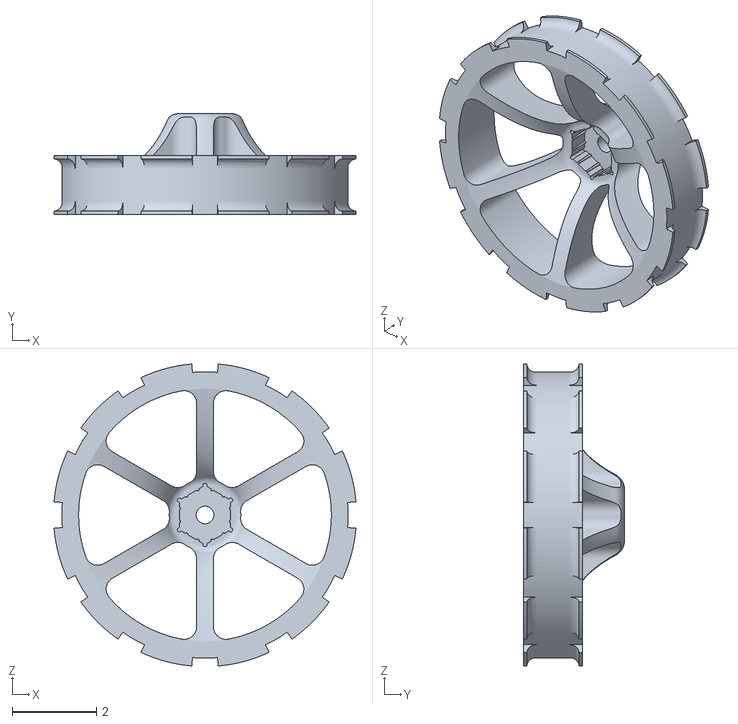
[picture p77: CAD file, 2024-03-27]
Construction/stl/wheel_5.stl
7.17 x 2.40 x 7.17
