akapustyanik/MZCAT/Construction/dxf/osvesh5.dxf

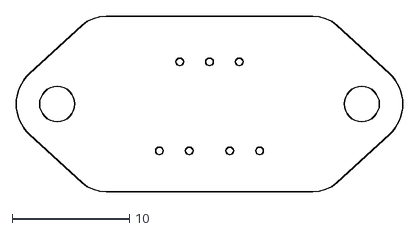
[picture p78: CAD file, 2024-03-27]
Construction/dxf/osvesh5.dxf
33.0 x 15.0
