akapustyanik/MZCAT/Construction/step/clik mate 5.stp

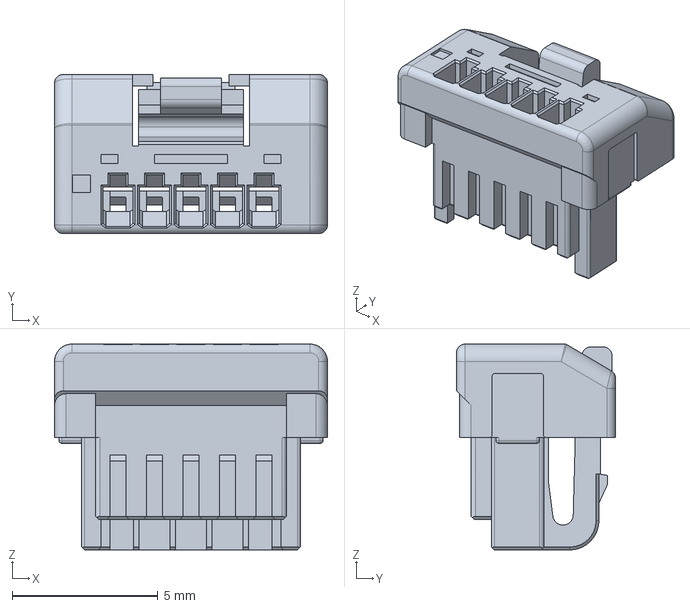
[picture p79: CAD file, 2024-03-27]
Construction/step/clik mate 5.stp
9.35 x 5.45 x 7.05 mm
