akapustyanik/MZCAT/Construction/stl/rolik.stl

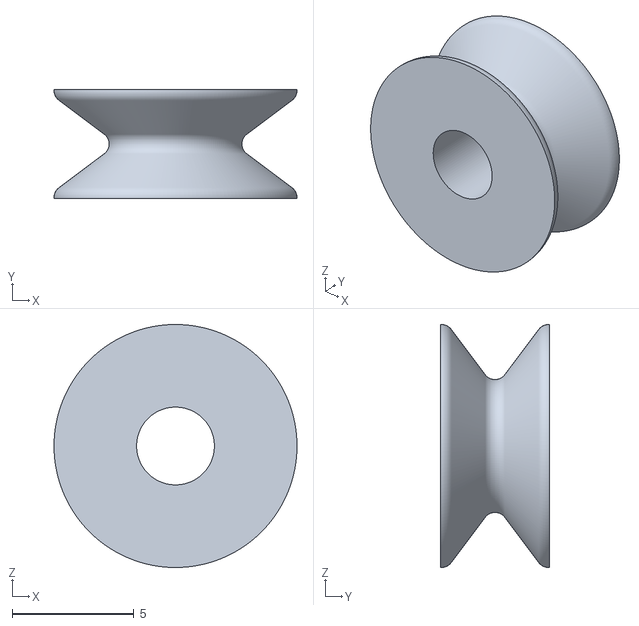
[picture p80: CAD file, 2024-03-27]
Construction/stl/rolik.stl
10.00 x 4.50 x 10.00
