akapustyanik/MZCAT/Construction/dxf/motherboard_countour2.dxf

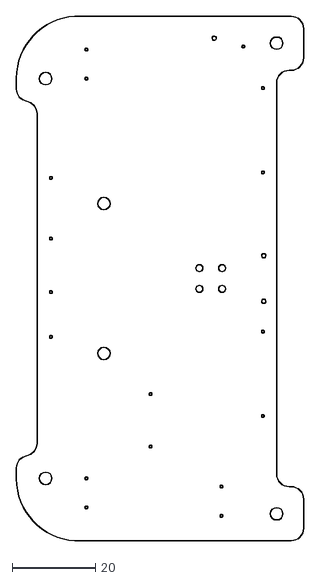
[picture p81: CAD file, 2024-03-27]
Construction/dxf/motherboard_countour2.dxf
69.0 x 126.0
