akapustyanik/MZCAT/Construction/other_models/OpenMV H7/Components/Crystal-SM2520-4.SLDPRT

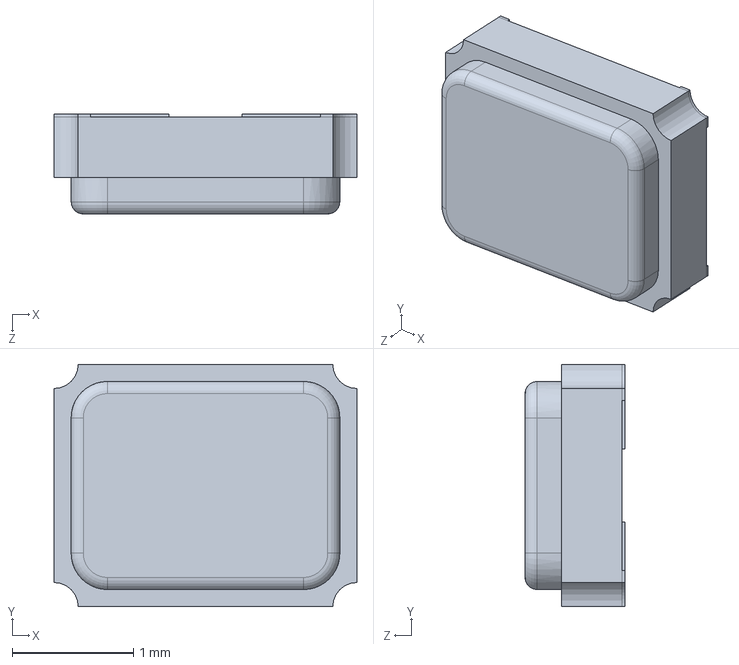
[picture p82: CAD file, 2024-03-27]
Construction/other_models/OpenMV H7/Components/Crystal-SM2520-4.SLDPRT
2.50 x 2.00 x 0.825 mm
