akapustyanik/MZCAT/Construction/stl/akkum3_base1.stl

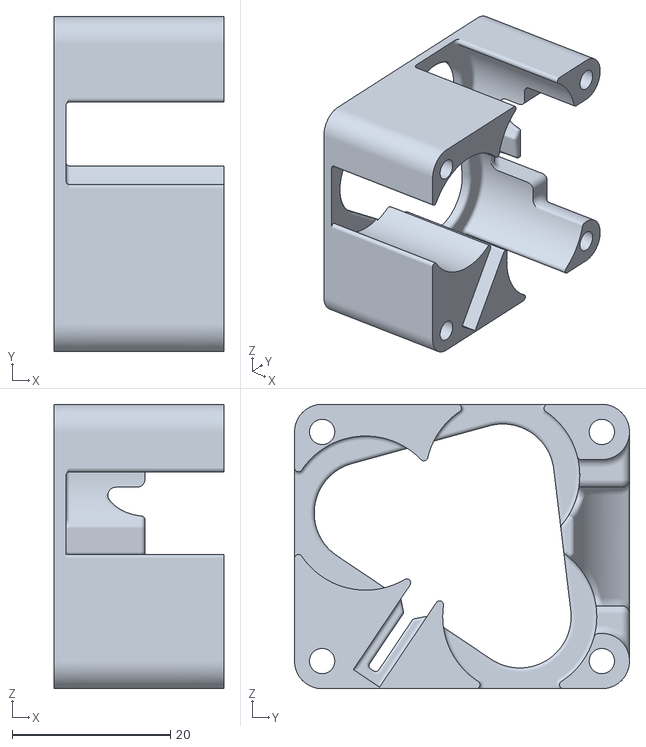
[picture p83: CAD file, 2024-03-27]
Construction/stl/akkum3_base1.stl
21.5 x 42.4 x 36.0
