akapustyanik/MZCAT/Construction/dxf/protection.dxf

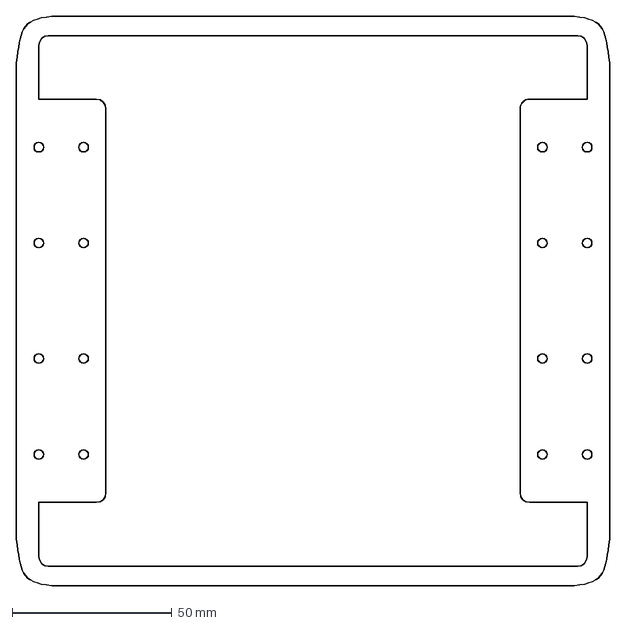
[picture p84: CAD file, 2024-03-27]
Construction/dxf/protection.dxf
185.5 x 178.0 mm
