akapustyanik/MZCAT/Construction/other_models/OpenMV H7/Components/DF12-36DS-0.5V.SLDPRT

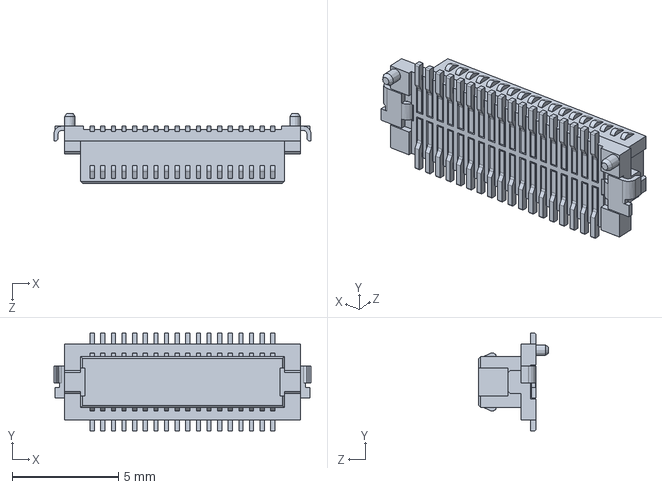
[picture p85: CAD file, 2024-03-27]
Construction/other_models/OpenMV H7/Components/DF12-36DS-0.5V.SLDPRT
12.1 x 4.60 x 3.30 mm
