akapustyanik/MZCAT/Construction/stl/User Library-640456-4.stl

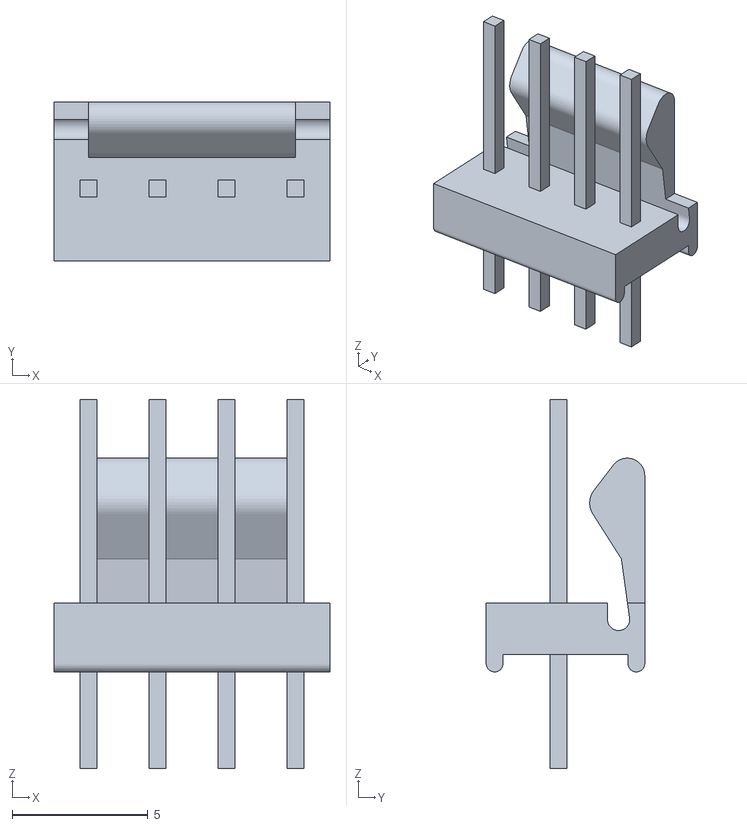
[picture p86: CAD file, 2024-03-27]
Construction/stl/User Library-640456-4.stl
10.2 x 5.84 x 13.6
