akapustyanik/MZCAT/Construction/dxf/akkum_frame.dxf

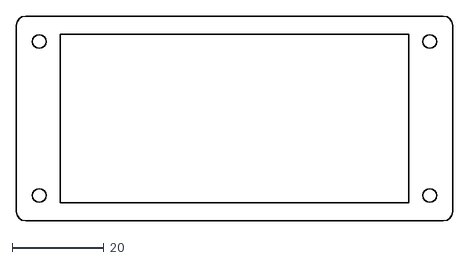
[picture p87: CAD file, 2024-03-27]
Construction/dxf/akkum_frame.dxf
95.2 x 44.7
