akapustyanik/MZCAT/Construction/other_models/OpenMV H7/Components/C0603K_C0603K.SLDPRT

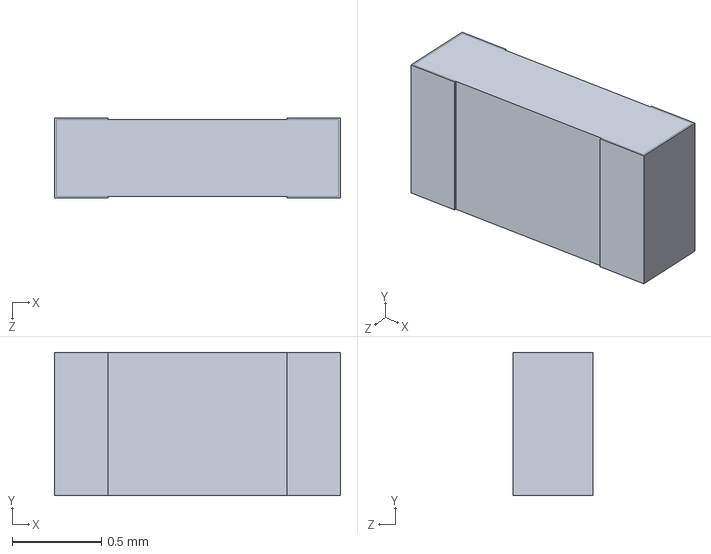
[picture p88: CAD file, 2024-03-27]
Construction/other_models/OpenMV H7/Components/C0603K_C0603K.SLDPRT
1.60 x 0.8 x 0.45 mm
