akapustyanik/MZCAT/Construction/stl/reyka_3.stl

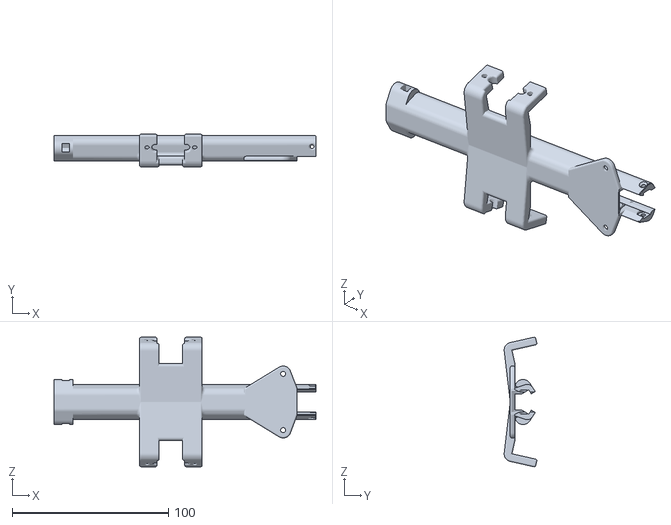
[picture p89: CAD file, 2024-03-27]
Construction/stl/reyka_3.stl
167.5 x 20.9 x 82.9
