akapustyanik/MZCAT/Construction/dxf/motherboard_countour3.dxf

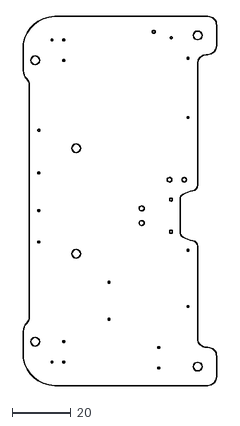
[picture p90: CAD file, 2024-03-27]
Construction/dxf/motherboard_countour3.dxf
66.0 x 126.0
