akapustyanik/MZCAT/Construction/other_models/OpenMV H7/Components/0805.SLDPRT

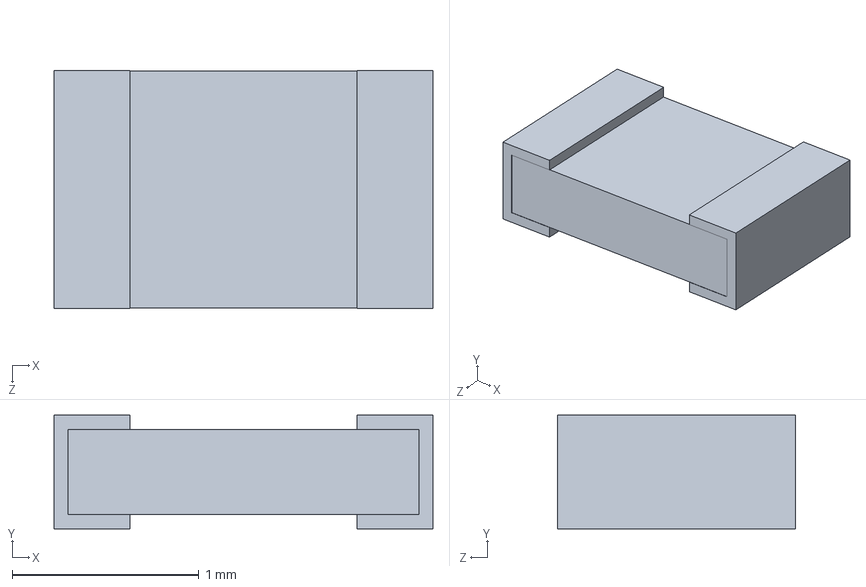
[picture p91: CAD file, 2024-03-27]
Construction/other_models/OpenMV H7/Components/0805.SLDPRT
2.03 x 0.61 x 1.28 mm
