akapustyanik/MZCAT/Construction/stl/tire ring_normal2.stl

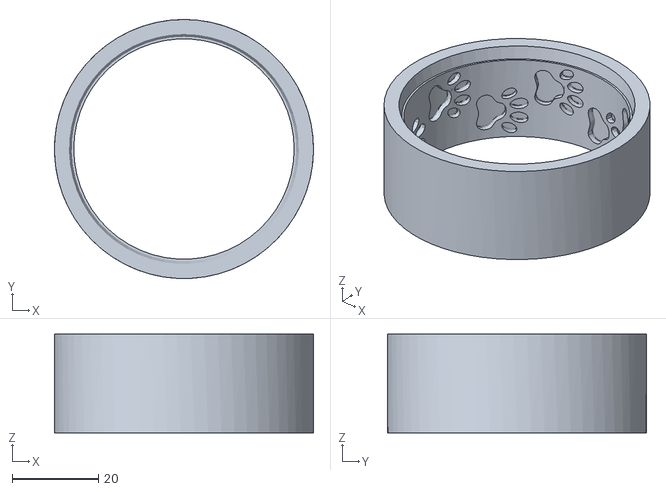
[picture p92: CAD file, 2024-03-27]
Construction/stl/tire ring_normal2.stl
60.0 x 60.0 x 22.9
