akapustyanik/MZCAT/Construction/dxf/protection_frame.dxf

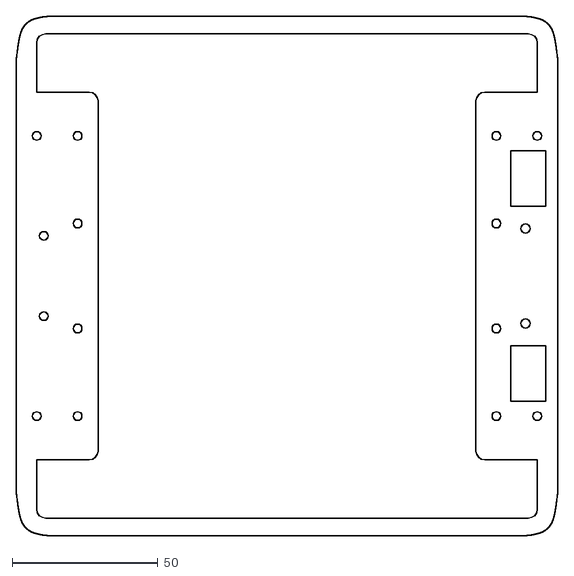
[picture p93: CAD file, 2024-03-27]
Construction/dxf/protection_frame.dxf
185.5 x 178.0
