akapustyanik/MZCAT/Construction/other_models/OpenMV H7/Components/CSP2-28.SLDPRT

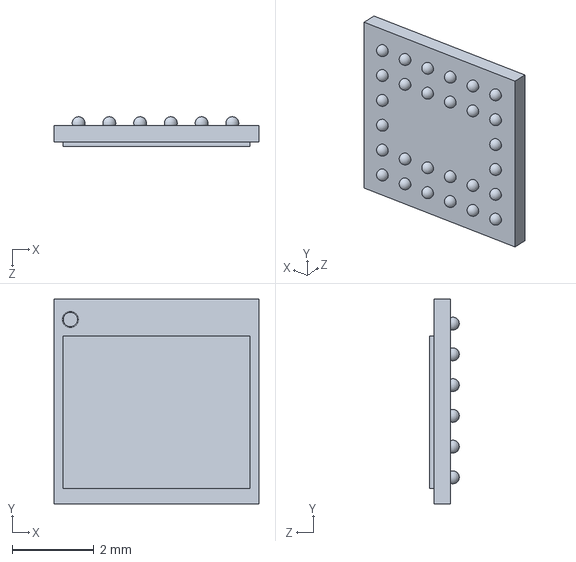
[picture p94: CAD file, 2024-03-27]
Construction/other_models/OpenMV H7/Components/CSP2-28.SLDPRT
5.00 x 5.00 x 0.724 mm
