akapustyanik/MZCAT/Construction/stl/block.stl

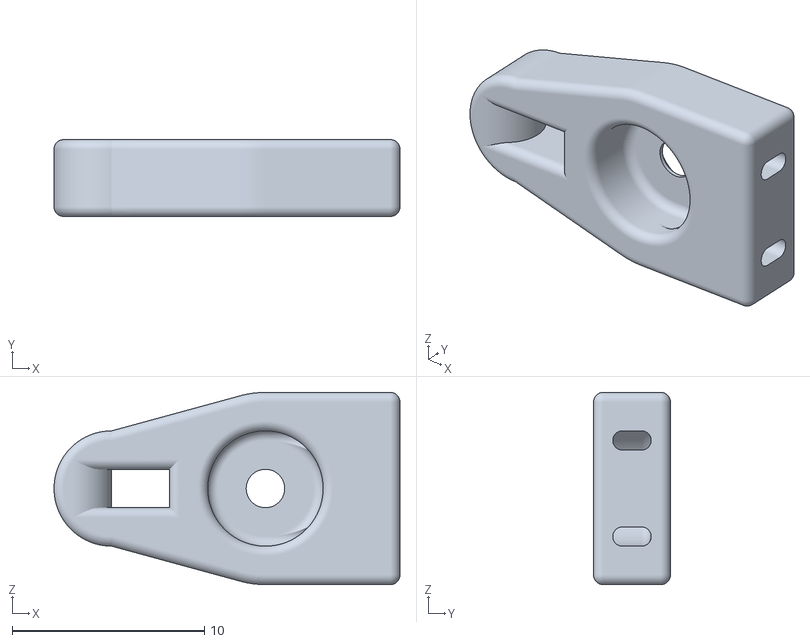
[picture p95: CAD file, 2024-03-27]
Construction/stl/block.stl
18.0 x 4.00 x 10.0
