akapustyanik/MZCAT/Construction/other_models/OpenMV H7/Components/SOT 23-5.SLDPRT

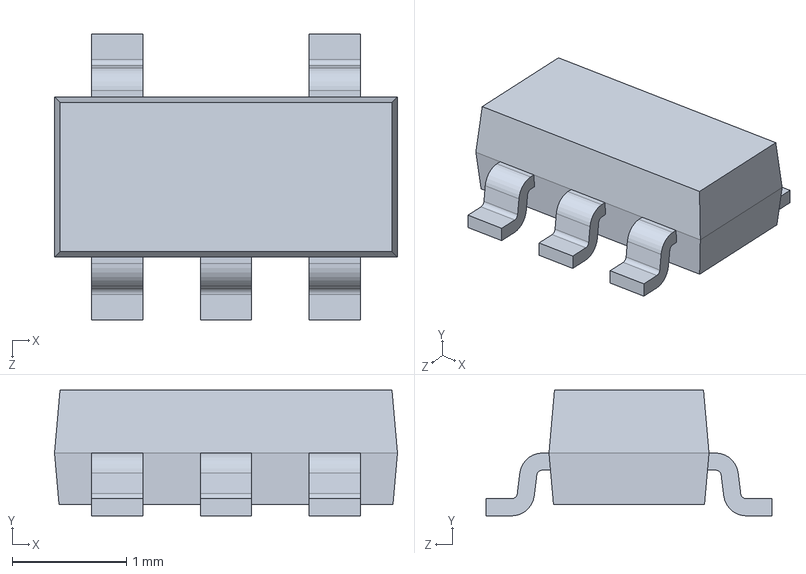
[picture p96: CAD file, 2024-03-27]
Construction/other_models/OpenMV H7/Components/SOT 23-5.SLDPRT
3.00 x 1.10 x 2.50 mm
