akapustyanik/MZCAT/Construction/stl/test_akkum_shelki.stl

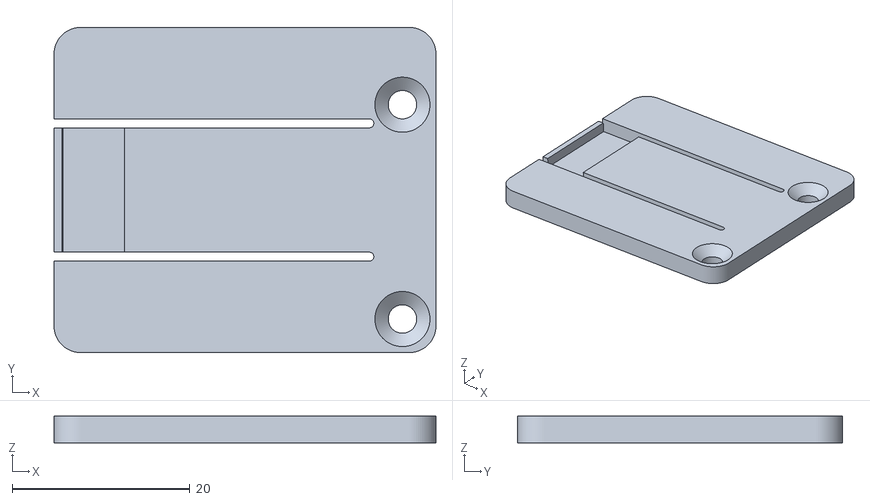
[picture p97: CAD file, 2024-03-27]
Construction/stl/test_akkum_shelki.stl
43.0 x 36.6 x 3.00
