akapustyanik/MZCAT/Construction/other_models/OpenMV H7/Components/SOD323_BAT54HT1G.SLDPRT

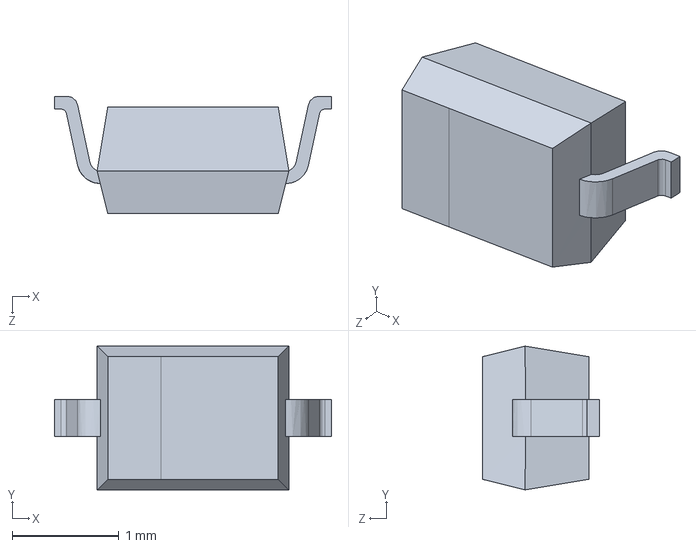
[picture p98: CAD file, 2024-03-27]
Construction/other_models/OpenMV H7/Components/SOD323_BAT54HT1G.SLDPRT
2.60 x 1.35 x 1.10 mm
