akapustyanik/MZCAT/Construction/stl/tire ring.stl

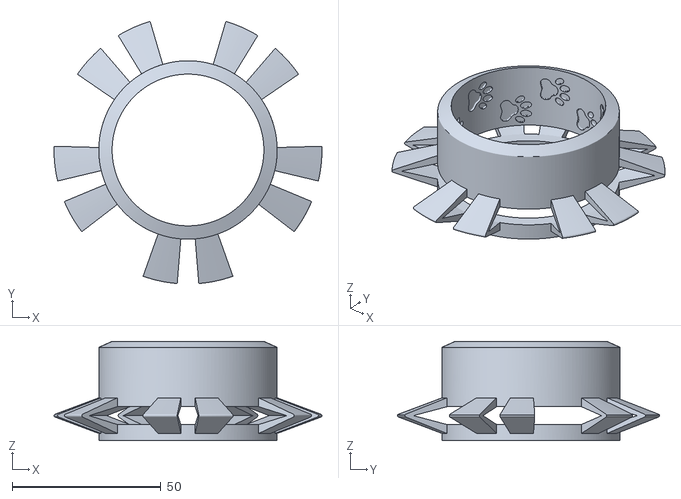
[picture p99: CAD file, 2024-03-27]
Construction/stl/tire ring.stl
90.2 x 88.2 x 33.4
