akapustyanik/MZCAT/Construction/stl/tire_cap3.stl

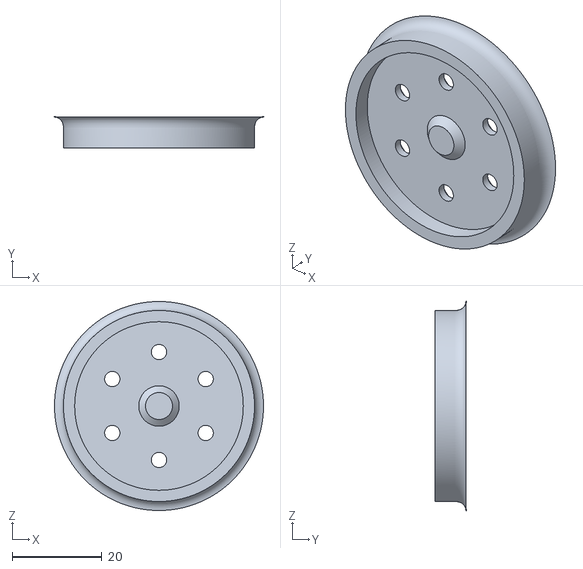
[picture p100: CAD file, 2024-03-27]
Construction/stl/tire_cap3.stl
46.5 x 6.95 x 46.5
