akapustyanik/MZCAT/Construction/stl/wheel_4.stl

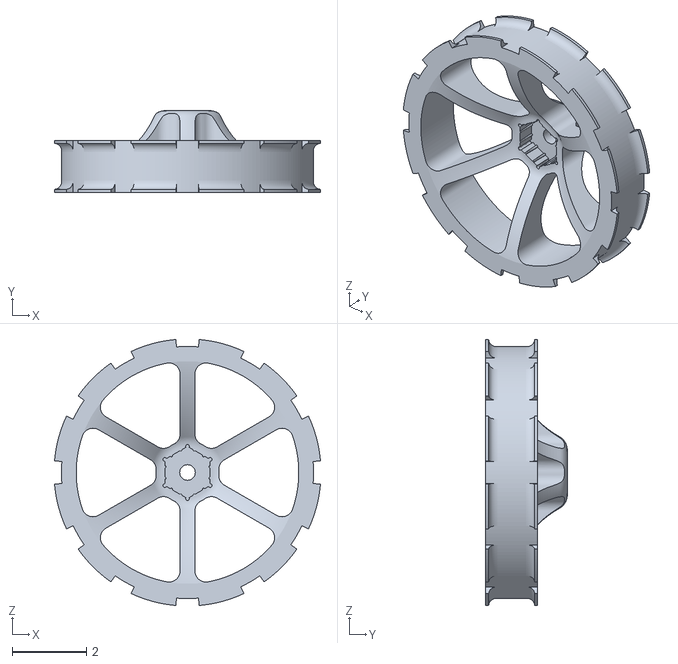
[picture p101: CAD file, 2024-03-27]
Construction/stl/wheel_4.stl
7.17 x 2.20 x 7.17
