akapustyanik/MZCAT/Construction/stl/laser_krepl_right.stl

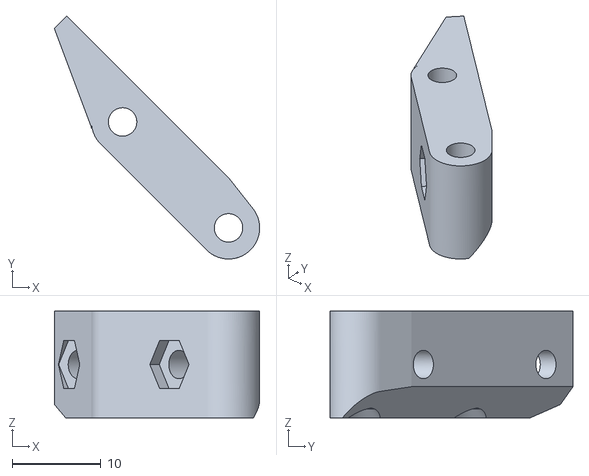
[picture p102: CAD file, 2024-03-27]
Construction/stl/laser_krepl_right.stl
23.1 x 27.3 x 12.0
