akapustyanik/MZCAT/Construction/stl/vagonetka_test.stl

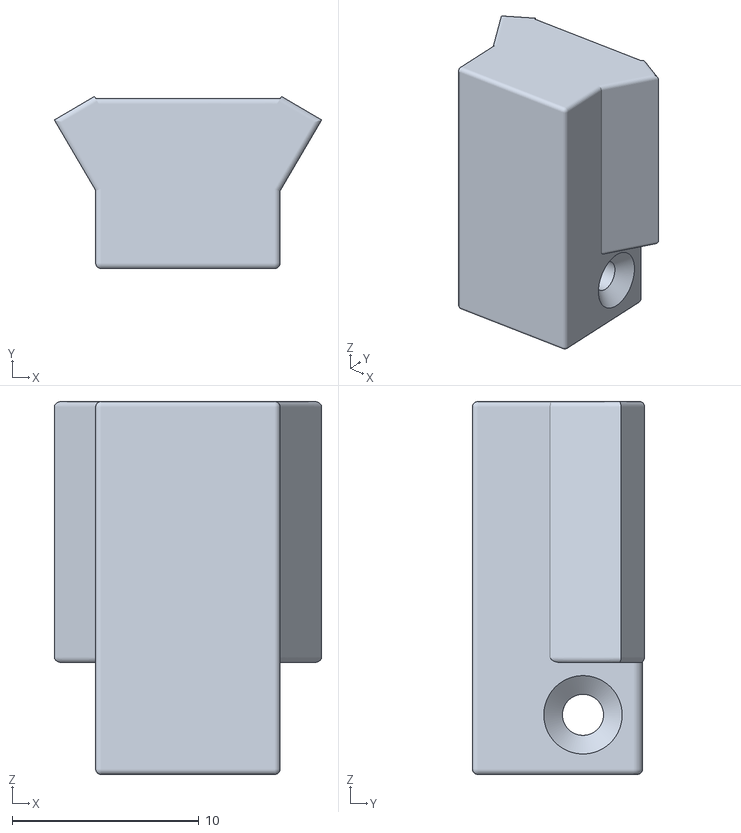
[picture p103: CAD file, 2024-03-27]
Construction/stl/vagonetka_test.stl
14.3 x 9.23 x 20.0
