akapustyanik/MZCAT/Construction/stl/rolik2_2.stl

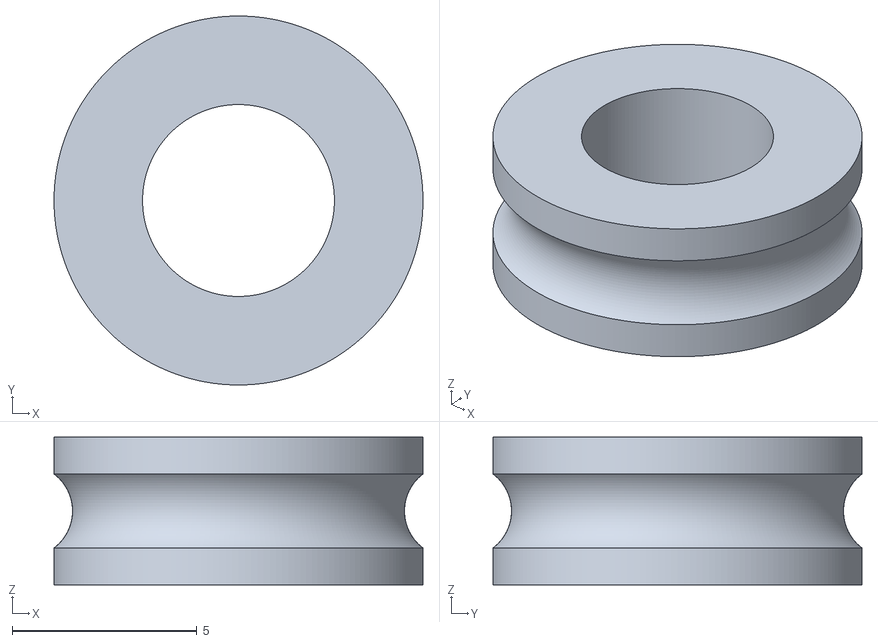
[picture p104: CAD file, 2024-03-27]
Construction/stl/rolik2_2.stl
10.0 x 10.0 x 4.00
