akapustyanik/MZCAT/Construction/stl/cap_end_cap.stl

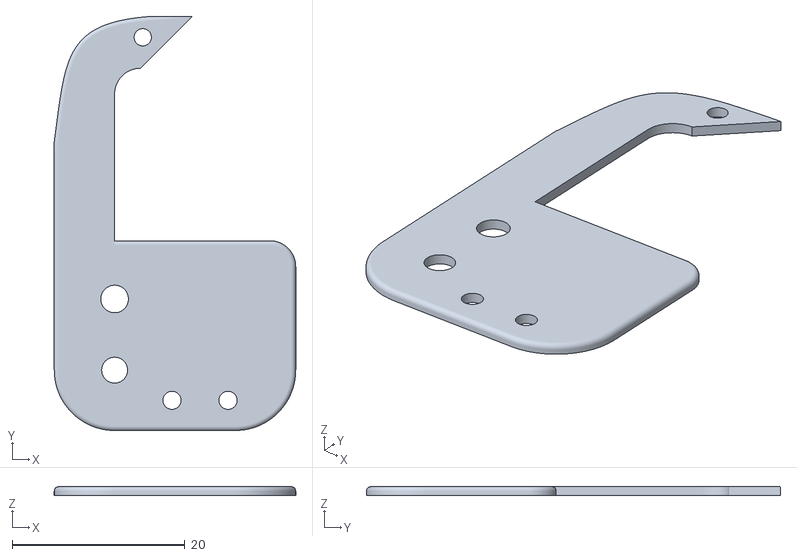
[picture p105: CAD file, 2024-03-27]
Construction/stl/cap_end_cap.stl
28.0 x 48.0 x 1.00
