akapustyanik/MZCAT/Construction/stl/button_krepl.stl

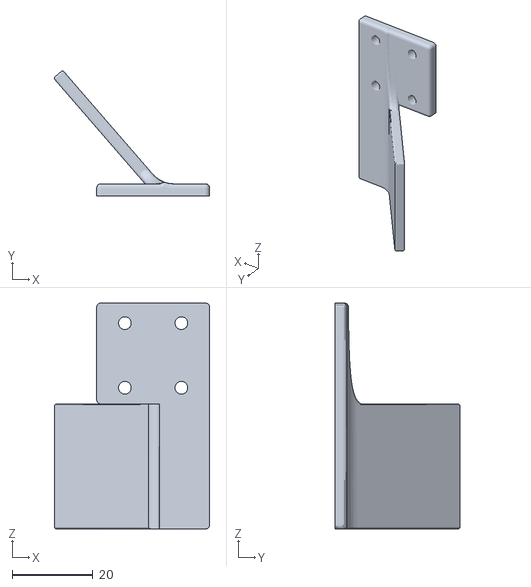
[picture p107: CAD file, 2024-03-27]
Construction/stl/button_krepl.stl
38.5 x 31.0 x 56.0
