akapustyanik/MZCAT/Construction/stl/cube.stl

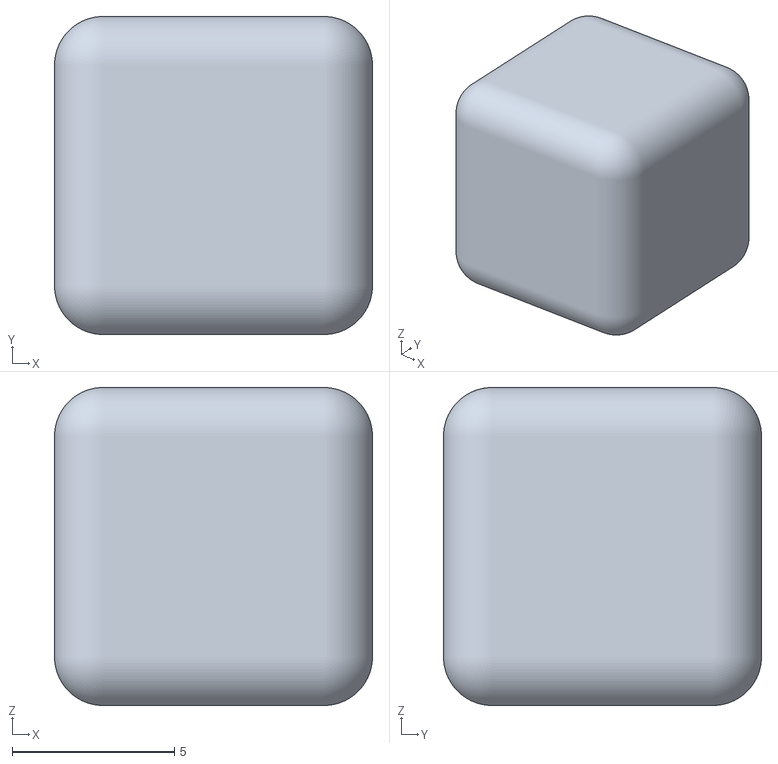
[picture p108: CAD file, 2024-03-27]
Construction/stl/cube.stl
9.80 x 9.80 x 9.80
