akapustyanik/MZCAT/Construction/stl/akkum_holder2.stl

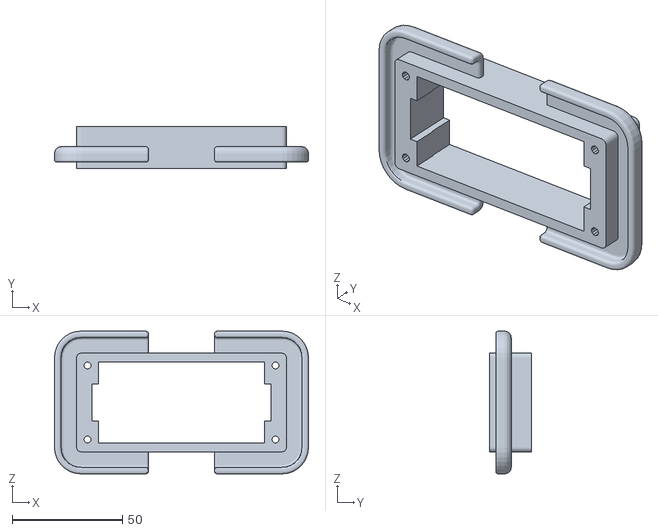
[picture p109: CAD file, 2024-03-27]
Construction/stl/akkum_holder2.stl
115.3 x 19.2 x 64.8
