akapustyanik/MZCAT/Construction/stl/wire_holder.stl

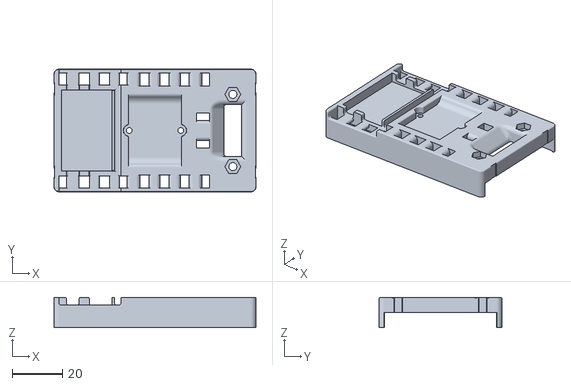
[picture p110: CAD file, 2024-03-27]
Construction/stl/wire_holder.stl
80.2 x 48.7 x 12.0
