akapustyanik/MZCAT/Construction/stl/shelki.stl

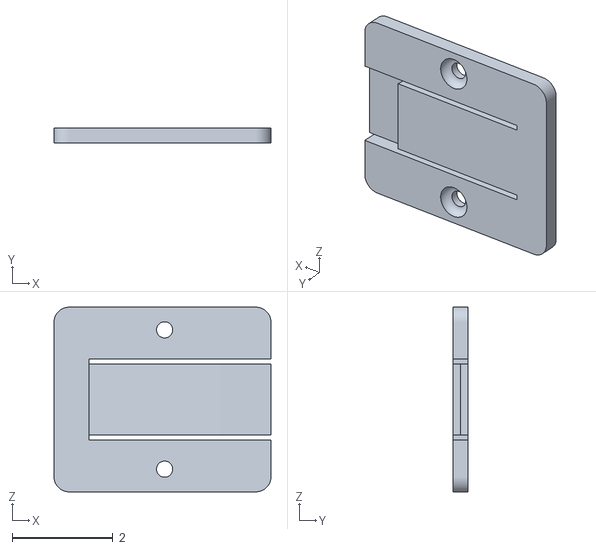
[picture p111: CAD file, 2024-03-27]
Construction/stl/shelki.stl
4.30 x 0.3 x 3.66
