akapustyanik/MZCAT/Construction/stl/cube3.stl

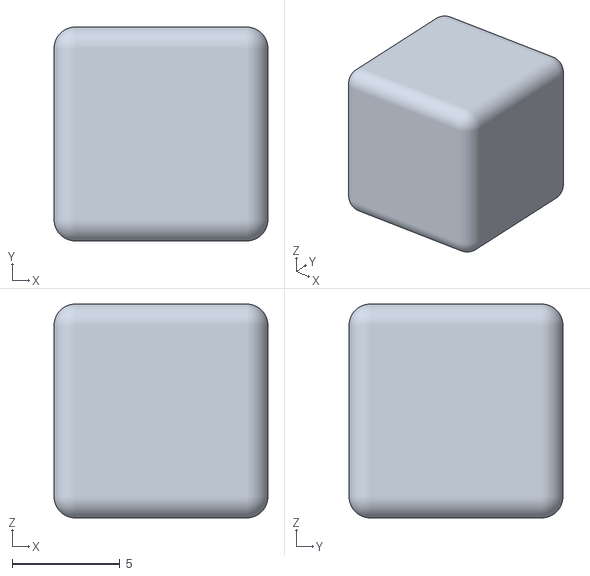
[picture p112: CAD file, 2024-03-27]
Construction/stl/cube3.stl
9.95 x 9.95 x 9.95
