akapustyanik/MZCAT/Construction/stl/pizza_3.stl

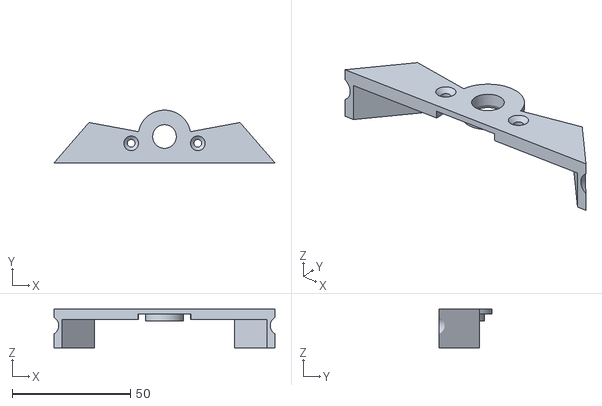
[picture p113: CAD file, 2024-03-27]
Construction/stl/pizza_3.stl
93.4 x 22.3 x 16.4
