akapustyanik/MZCAT/Construction/stl/fast_test_akkum_2.stl

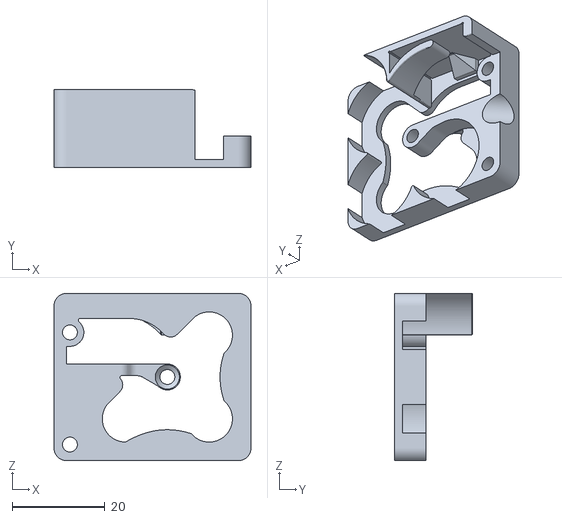
[picture p114: CAD file, 2024-03-27]
Construction/stl/fast_test_akkum_2.stl
42.4 x 16.7 x 36.0
