akapustyanik/MZCAT/Construction/stl/Arduino_Mega_2560_-_STL.stl

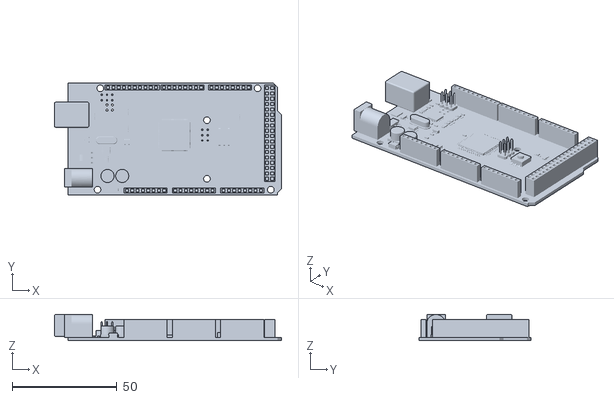
[picture p115: CAD file, 2024-03-27]
Construction/stl/Arduino_Mega_2560_-_STL.stl
108.1 x 53.3 x 12.5
