akapustyanik/MZCAT/Construction/stl/fast_battery_2.stl

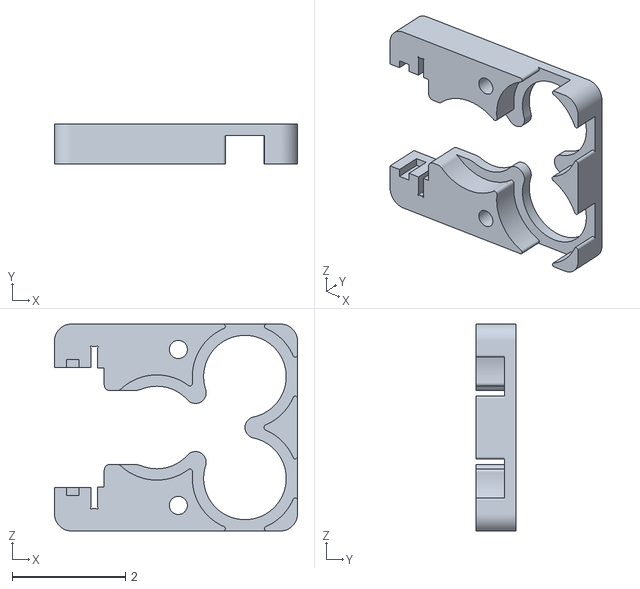
[picture p116: CAD file, 2024-03-27]
Construction/stl/fast_battery_2.stl
4.30 x 0.7 x 3.66
