akapustyanik/MZCAT/Construction/stl/light_sens_krepl.stl

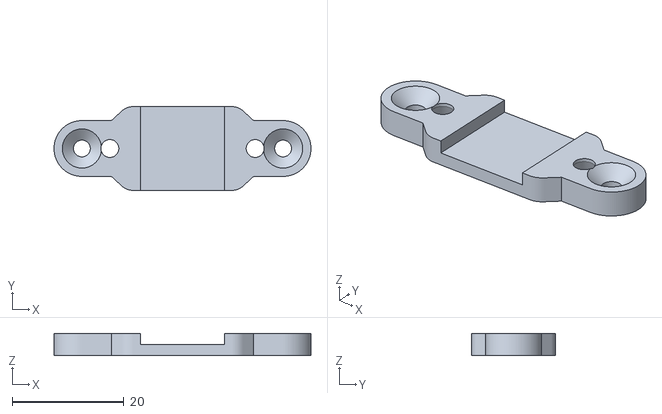
[picture p117: CAD file, 2024-03-27]
Construction/stl/light_sens_krepl.stl
46.0 x 15.0 x 4.00
