akapustyanik/MZCAT/Construction/stl/end_cap.stl

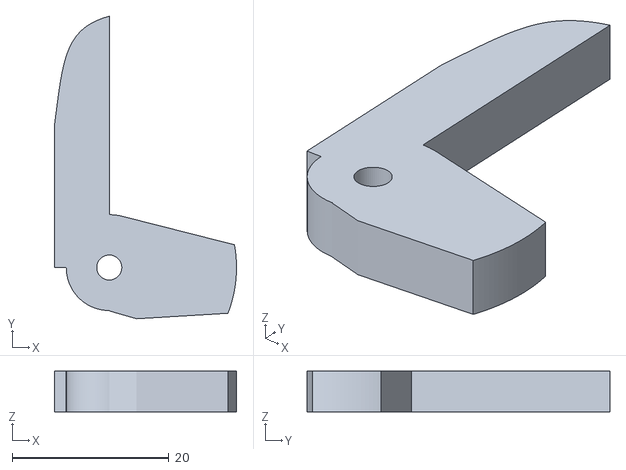
[picture p118: CAD file, 2024-03-27]
Construction/stl/end_cap.stl
23.3 x 38.7 x 5.20
