akapustyanik/MZCAT/Construction/stl/защёлка_выдача.stl

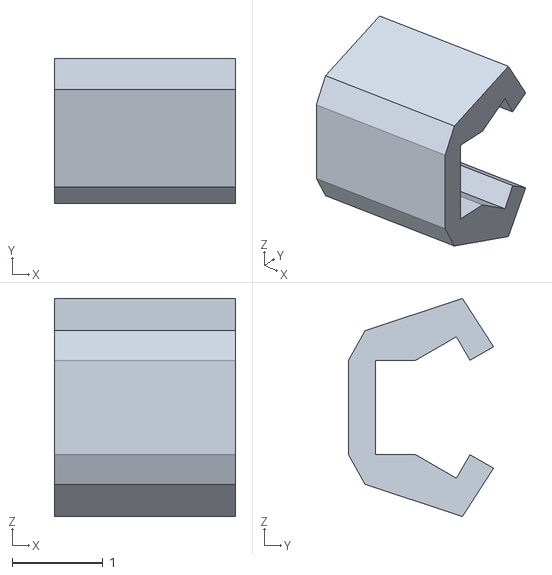
[picture p119: CAD file, 2024-03-27]
Construction/stl/защёлка_выдача.stl
2.00 x 1.60 x 2.40
