akapustyanik/MZCAT/Construction/stl/minirolik.stl

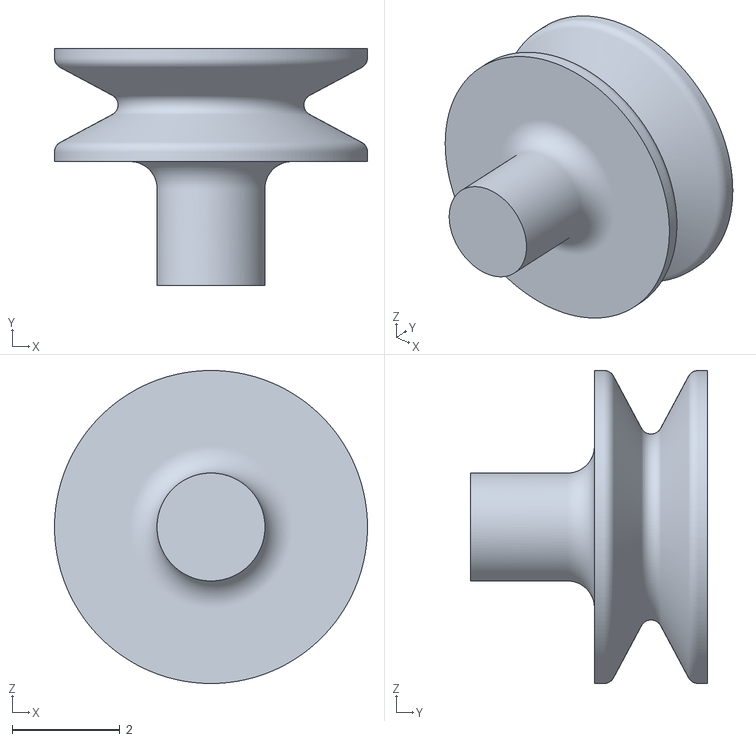
[picture p120: CAD file, 2024-03-27]
Construction/stl/minirolik.stl
5.80 x 4.40 x 5.80
