akapustyanik/MZCAT/Construction/stl/switch_krepl.stl

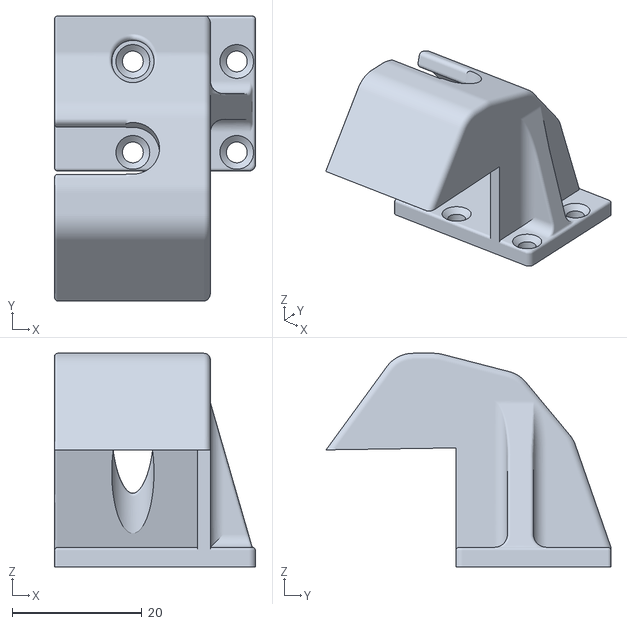
[picture p121: CAD file, 2024-03-27]
Construction/stl/switch_krepl.stl
30.9 x 43.9 x 32.9
