akapustyanik/MZCAT/Construction/stl/tire disk.stl

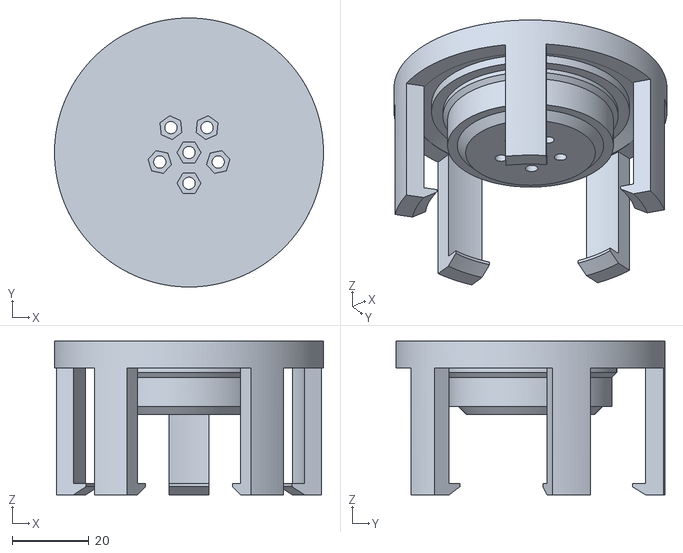
[picture p122: CAD file, 2024-03-27]
Construction/stl/tire disk.stl
70.0 x 70.0 x 40.0
