akapustyanik/MZCAT/Construction/stl/block_02.stl

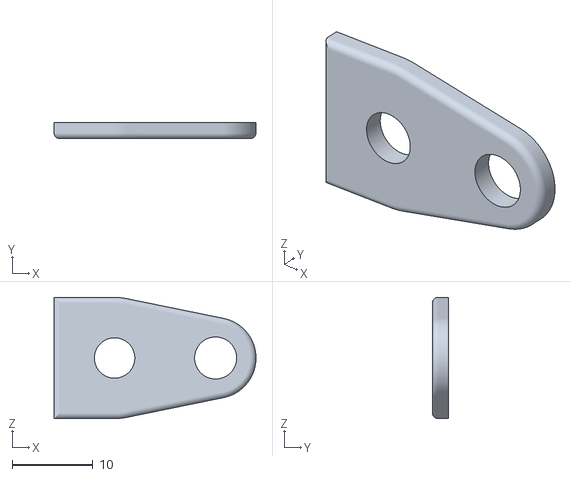
[picture p123: CAD file, 2024-03-27]
Construction/stl/block_02.stl
25.0 x 2.00 x 15.0
