akapustyanik/MZCAT/Construction/stl/pizza.stl

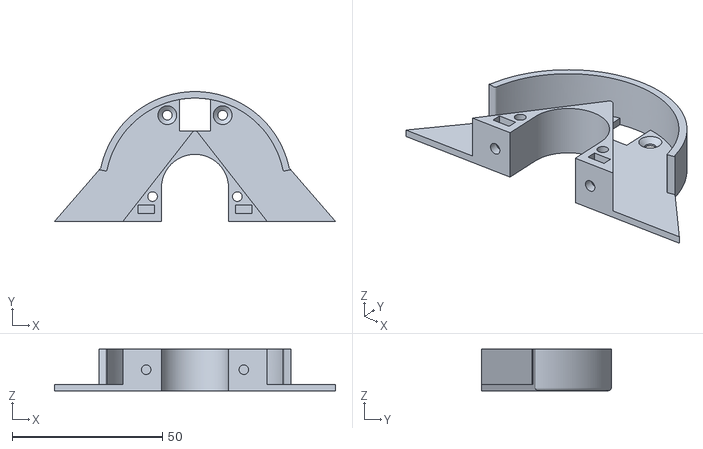
[picture p124: CAD file, 2024-03-27]
Construction/stl/pizza.stl
93.4 x 43.1 x 13.8
