akapustyanik/MZCAT/Construction/stl/pizza_disk.stl

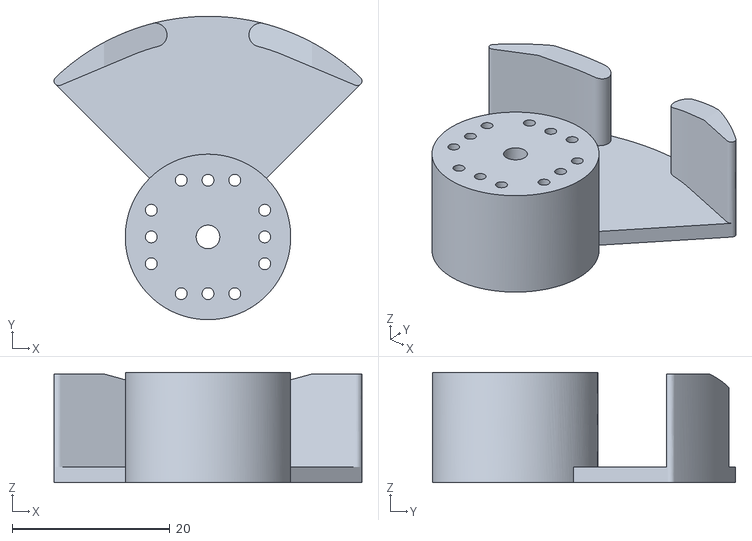
[picture p125: CAD file, 2024-03-27]
Construction/stl/pizza_disk.stl
39.1 x 38.5 x 14.0
