akapustyanik/MZCAT/Construction/stl/tire_cap2.stl

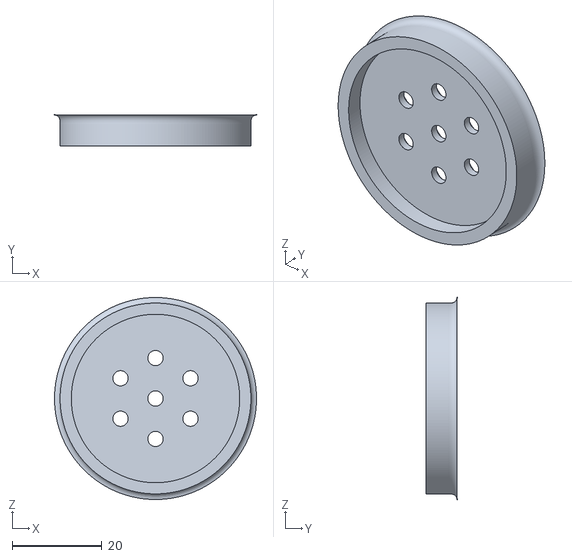
[picture p126: CAD file, 2024-03-27]
Construction/stl/tire_cap2.stl
45.0 x 6.95 x 45.0
