akapustyanik/MZCAT/Construction/stl/lid.stl

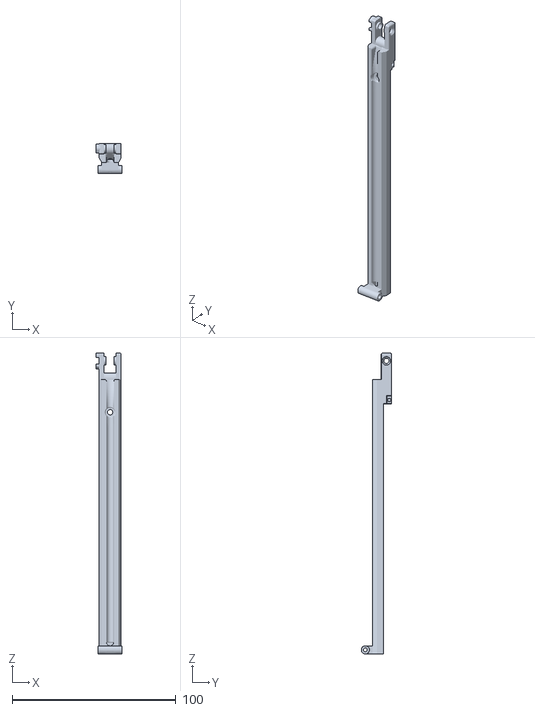
[picture p127: CAD file, 2024-03-27]
Construction/stl/lid.stl
16.0 x 18.6 x 183.7
