akapustyanik/MZCAT/Construction/stl/vydacha_krepl_serv.stl

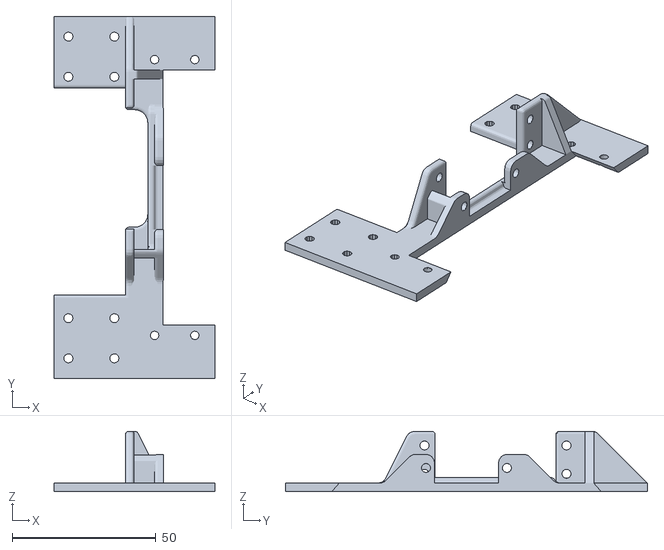
[picture p128: CAD file, 2024-03-27]
Construction/stl/vydacha_krepl_serv.stl
56.0 x 126.0 x 21.0
