akapustyanik/MZCAT/Construction/stl/derjatel_HDD.stl

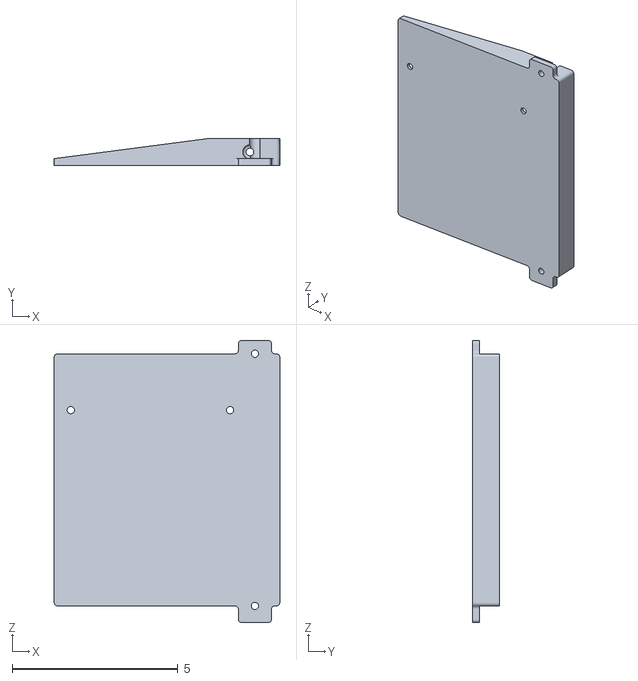
[picture p129: CAD file, 2024-03-27]
Construction/stl/derjatel_HDD.stl
6.80 x 0.8 x 8.50
