akapustyanik/MZCAT/Construction/stl/derjatel_HDD_3.stl

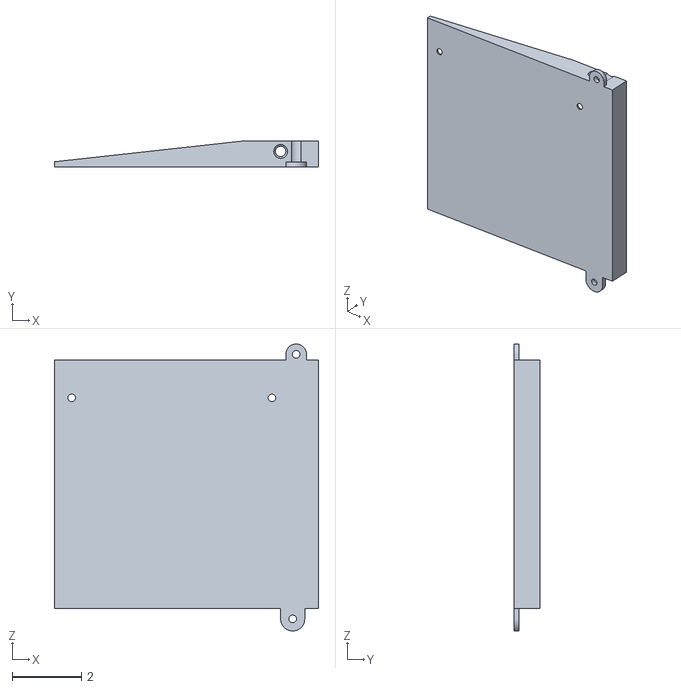
[picture p130: CAD file, 2024-03-27]
Construction/stl/derjatel_HDD_3.stl
7.65 x 0.75 x 8.31
