akapustyanik/MZCAT/Construction/stl/71y6037_2129691-1.stl

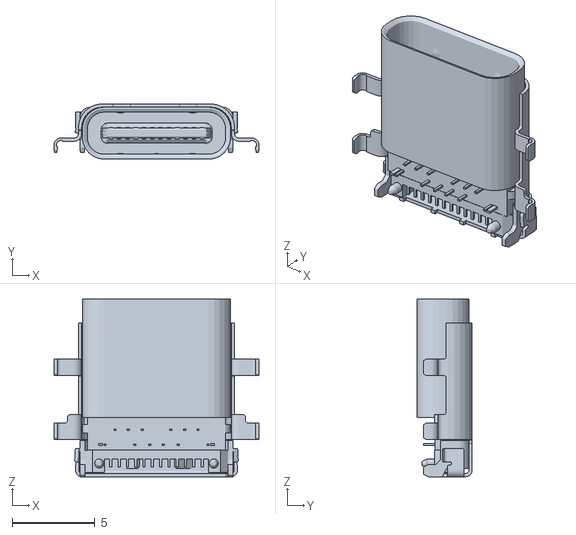
[picture p131: CAD file, 2024-03-27]
Construction/stl/71y6037_2129691-1.stl
12.4 x 3.34 x 10.7
