akapustyanik/MZCAT/Construction/stl/cube2.stl

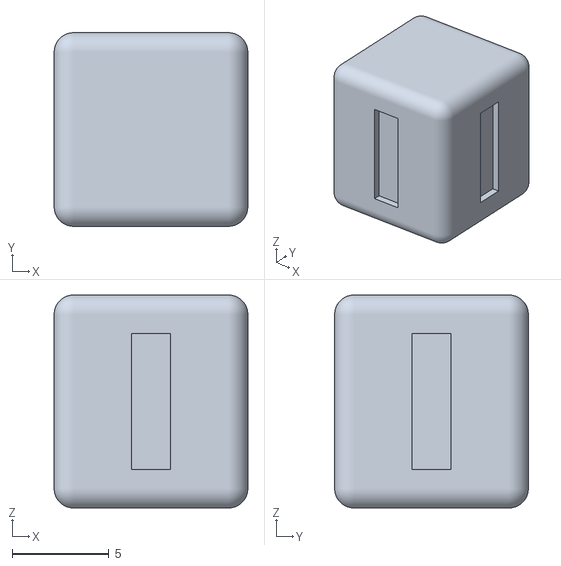
[picture p132: CAD file, 2024-03-27]
Construction/stl/cube2.stl
10.0 x 10.0 x 11.0
