akapustyanik/MZCAT/Construction/stl/tire cap.stl

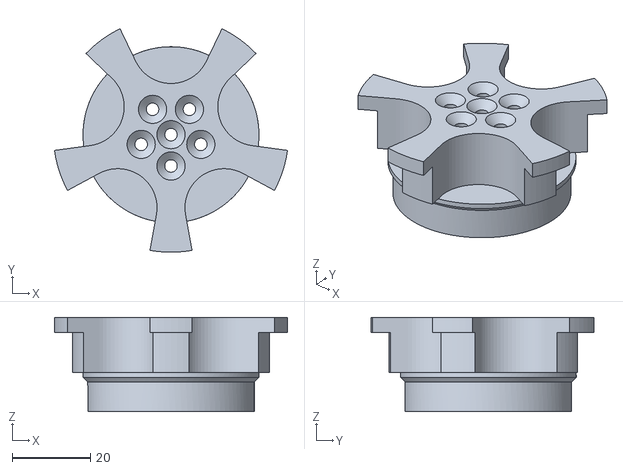
[picture p133: CAD file, 2024-03-27]
Construction/stl/tire cap.stl
59.5 x 57.0 x 24.0
