akapustyanik/MZCAT/Construction/stl/fast_test_akkum_1.stl

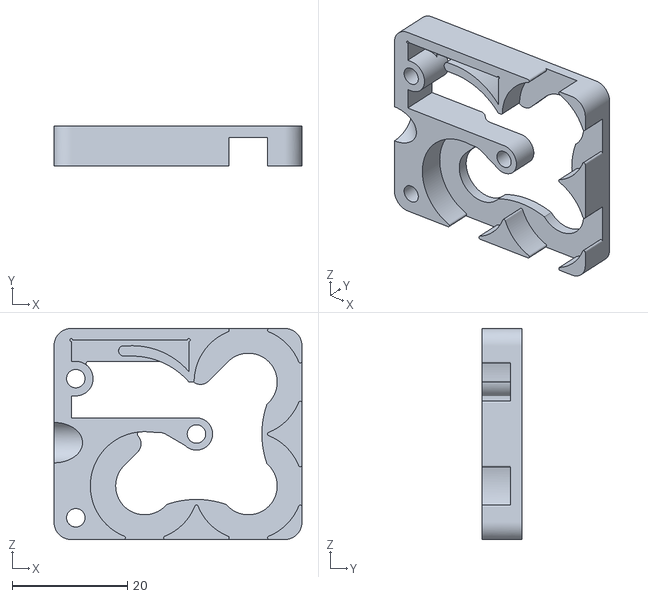
[picture p134: CAD file, 2024-03-27]
Construction/stl/fast_test_akkum_1.stl
43.0 x 7.00 x 36.6
