akapustyanik/MZCAT/Construction/stl/reyka.stl

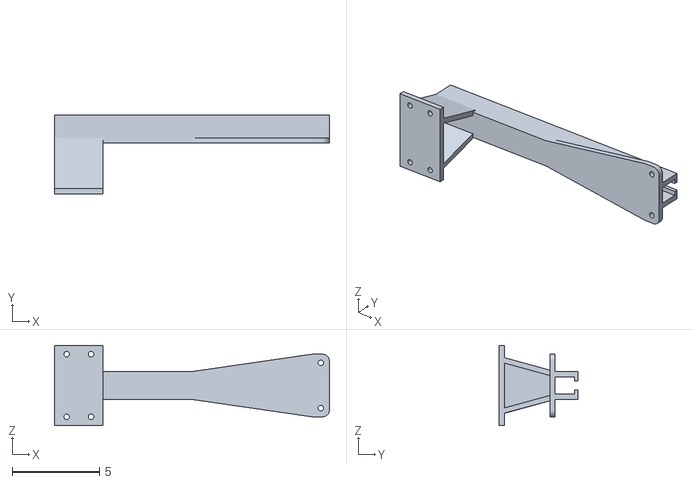
[picture p135: CAD file, 2024-03-27]
Construction/stl/reyka.stl
15.8 x 4.51 x 4.60
