akapustyanik/MZCAT/Construction/stl/User Library-640456-3.stl

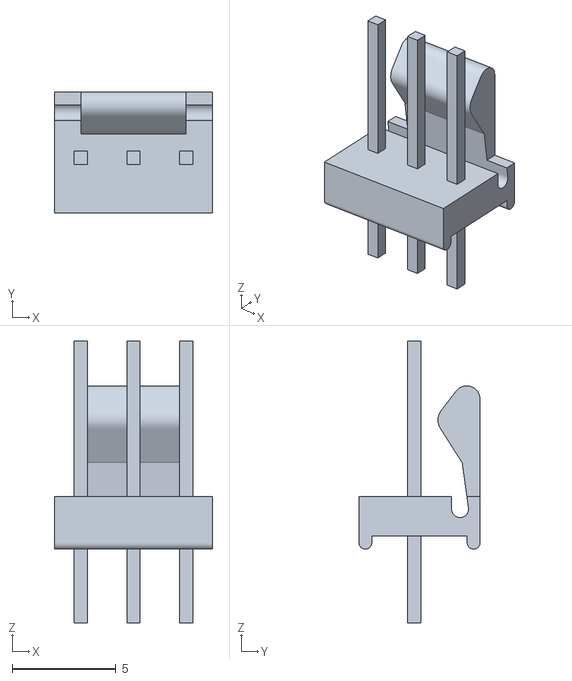
[picture p136: CAD file, 2024-03-27]
Construction/stl/User Library-640456-3.stl
7.62 x 5.84 x 13.6
