akapustyanik/MZCAT/Construction/stl/blochek.stl

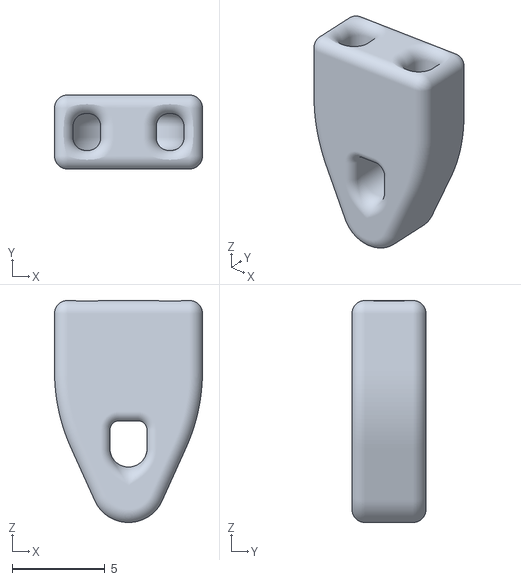
[picture p137: CAD file, 2024-03-27]
Construction/stl/blochek.stl
8.00 x 4.00 x 12.0
