akapustyanik/MZCAT/Construction/stl/block_01.stl

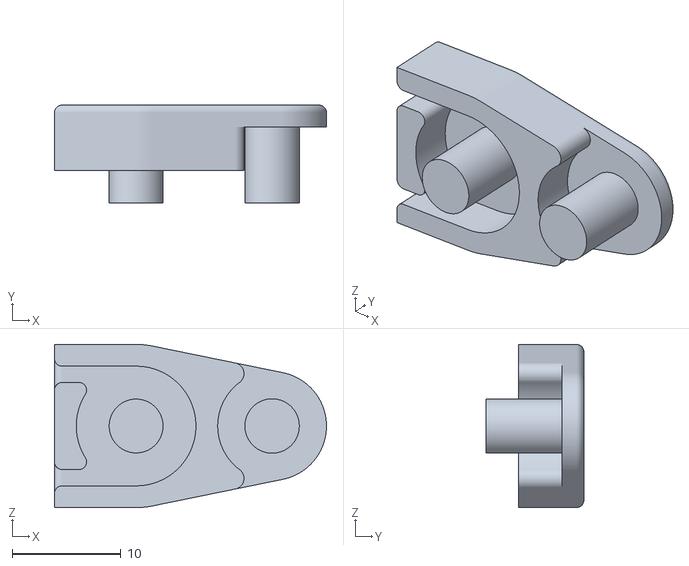
[picture p138: CAD file, 2024-03-27]
Construction/stl/block_01.stl
25.0 x 9.00 x 15.0
