akapustyanik/MZCAT/Construction/stl/tire vtulka.stl

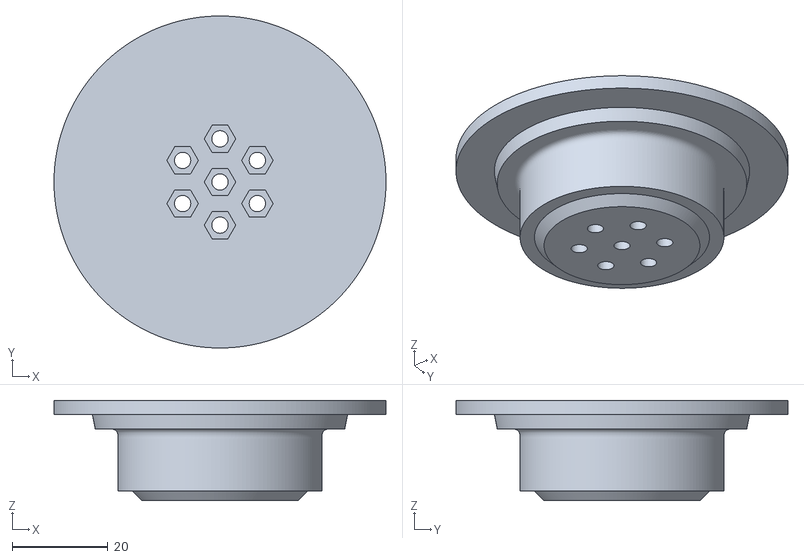
[picture p139: CAD file, 2024-03-27]
Construction/stl/tire vtulka.stl
69.2 x 69.2 x 20.9
