akapustyanik/MZCAT/Construction/stl/держатель_гаек.stl

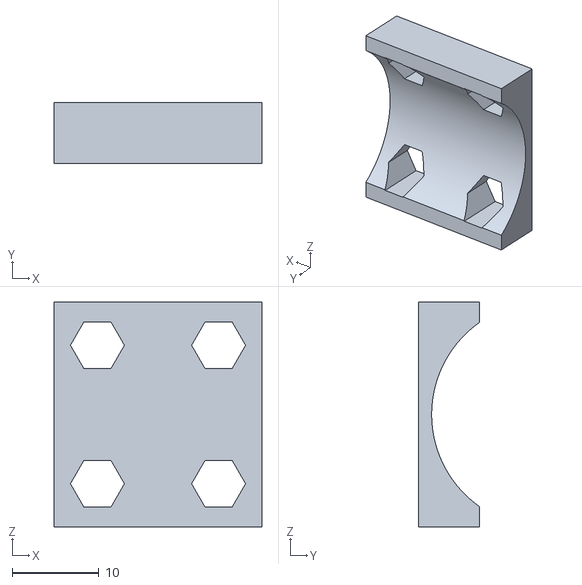
[picture p140: CAD file, 2024-03-27]
Construction/stl/держатель_гаек.stl
24.0 x 7.00 x 26.0
