akapustyanik/MZCAT/Construction/stl/fast_test_akkum.stl

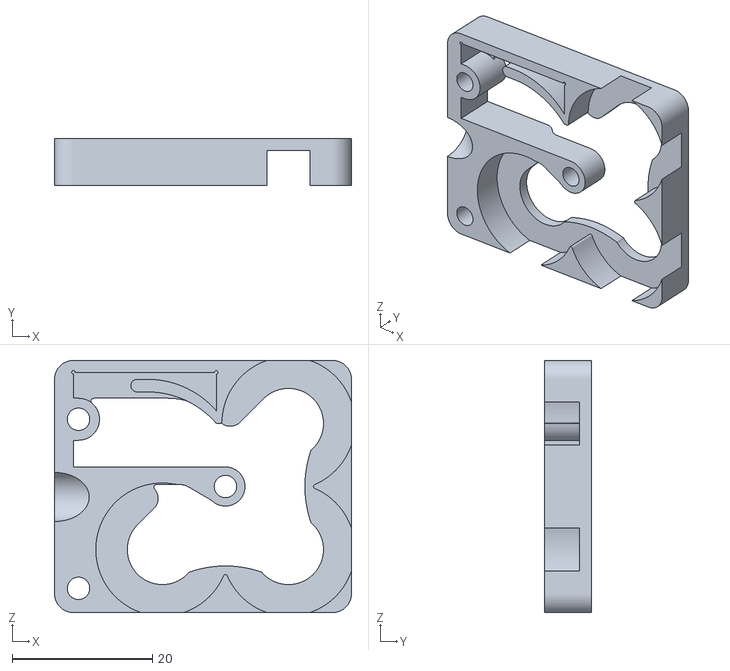
[picture p141: CAD file, 2024-03-27]
Construction/stl/fast_test_akkum.stl
42.4 x 6.70 x 36.0
