akapustyanik/MZCAT/Construction/other_models/cherrry red/cherry.JPG

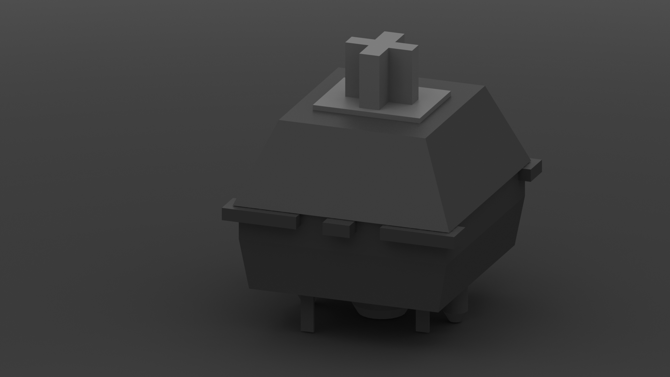
Construction/other_models/cherrry red/cherry.JPG
