akapustyanik/MZCAT/Construction/other_models/MG996R/datasheet.png

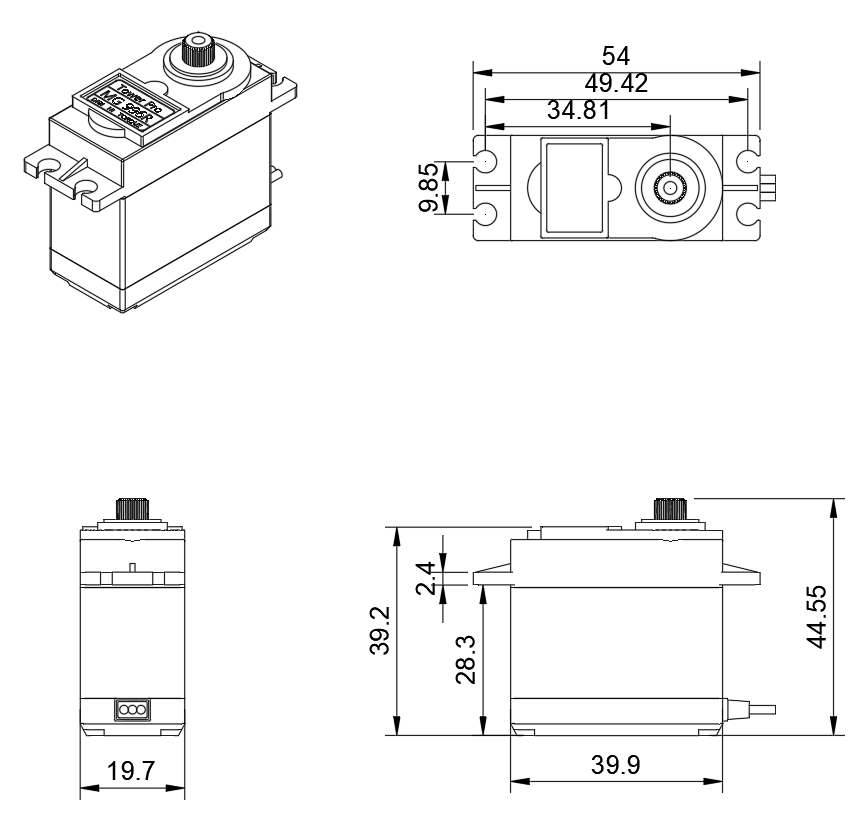
Construction/other_models/MG996R/datasheet.png
