akapustyanik/MZCAT/Construction/other_models/MG996R/others.png

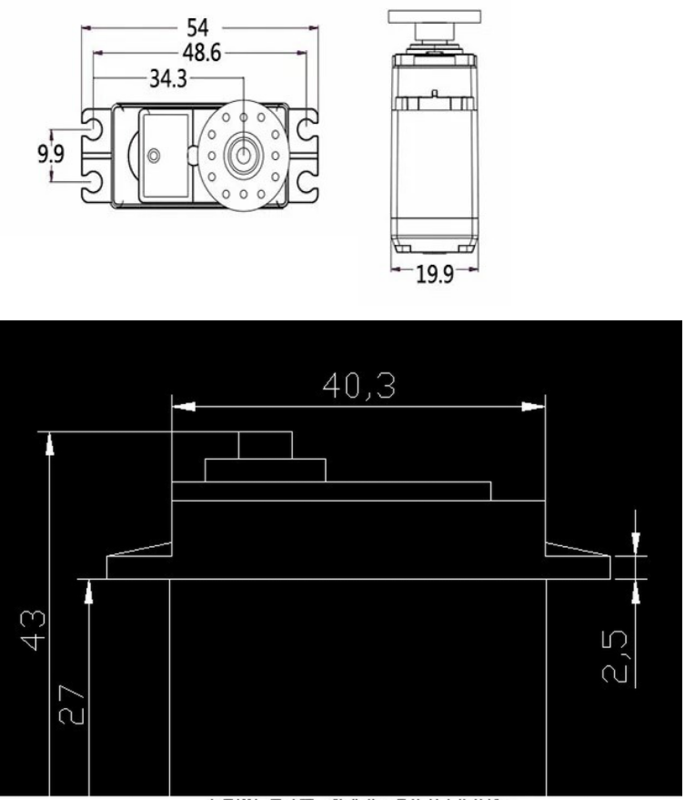
Construction/other_models/MG996R/others.png
