akapustyanik/MZCAT/Construction/other_models/OpenMV H7/Render1.jpg

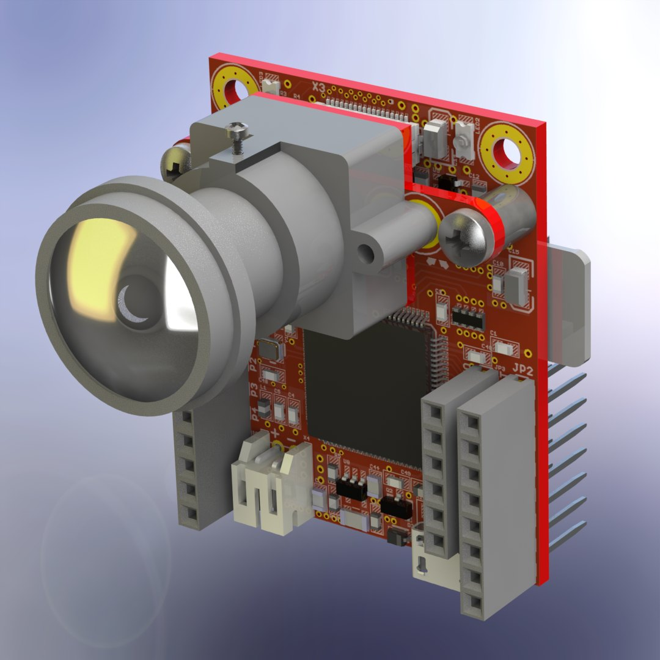
Construction/other_models/OpenMV H7/Render1.jpg
