akapustyanik/MZCAT/Construction/other_models/OpenMV H7/Render2.jpg

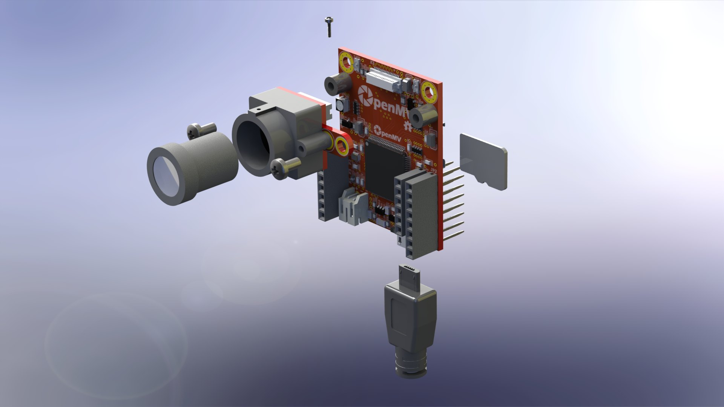
Construction/other_models/OpenMV H7/Render2.jpg
