akapustyanik/MZCAT/Construction/other_models/vl53l0x/view 2.JPG

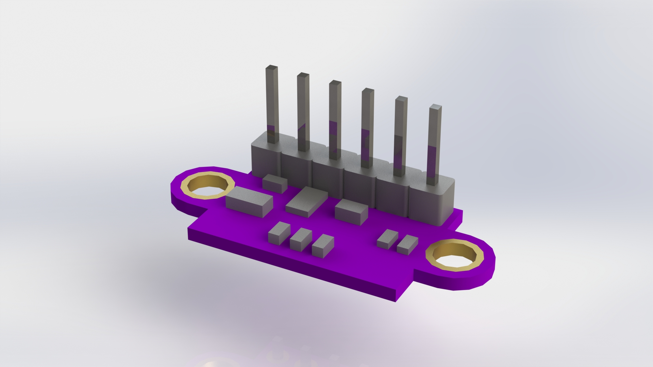
Construction/other_models/vl53l0x/view 2.JPG
